lora-gateway/esxp1302/main/packet_forwarder/lora_pkt_fwd.c

/*
 / _____)             _              | |
( (____  _____ ____ _| |_ _____  ____| |__
 \____ \| ___ |    (_   _) ___ |/ ___)  _ \
 _____) ) ____| | | || |_| ____( (___| | | |
(______/|_____)_|_|_| \__)_____)\____)_| |_|
  (C)2019 Semtech

Description:
    Configure Lora concentrator and forward packets to a server
    Use GPS for packet timestamping.
    Send a becon at a regular interval without server intervention

License: Revised BSD License, see LICENSE.TXT file include in the project
*/


/* fix an issue between POSIX and C99 */
#if __STDC_VERSION__ >= 199901L
    #define _XOPEN_SOURCE 600
#else
    #define _XOPEN_SOURCE 500
#endif

#include <stdint.h>         /* C99 types */
#include <stdbool.h>        /* bool type */
#include <stdio.h>          /* printf, fprintf, snprintf, fopen, fputs */
#include <inttypes.h>       /* PRIx64, PRIu64... */

#include <string.h>         /* memset */
#include <signal.h>         /* sigaction */
#include <time.h>           /* time, clock_gettime, strftime, gmtime */
#include <sys/time.h>       /* timeval */
#include <unistd.h>         /* getopt, access */
#include <stdlib.h>         /* atoi, exit */
#include <errno.h>          /* error messages */
#include <math.h>           /* modf */

#include <sys/socket.h>     /* socket specific definitions */
#include <netinet/in.h>     /* INET constants and stuff */
#include <arpa/inet.h>      /* IP address conversion stuff */
#include <netdb.h>          /* gai_strerror */

#include <pthread.h>

#include "trace.h"
#include "jitqueue.h"
#include "parson.h"
#include "base64.h"
#include "loragw_hal.h"
#include "loragw_aux.h"
#include "loragw_reg.h"
#include "loragw_gps.h"
#include "loragw_gpio.h"

/// For ESP32
#include "freertos/FreeRTOS.h"
#include "freertos/task.h"
#include "freertos/semphr.h"
#include "freertos/event_groups.h"
#include "esp_system.h"
#include "esp_wifi.h"
#include "esp_event.h"
#include "esp_log.h"
#include "esp_err.h"
#include "nvs_flash.h"
#include "esp_console.h"
#include "argtable3/argtable3.h"
#include "esp_netif.h"
#include "esp_timer.h"
#include "esp_mac.h"
#include "esp_rom_gpio.h"
#include "mqtt_client.h"

#include "lwip/err.h"
#include "lwip/sys.h"
#include "lwip/sockets.h"
#include <lwip/netdb.h>
#include "esp_sntp.h"

#include "global_json.h"
#include "driver/gpio.h"

#include "http_server.h"
#include "led_indication.h"
#include "ioe.h"
#include "web_config.h"
#include "loragw_version.h"


#define ARRAY_SIZE(a)   (sizeof(a) / sizeof((a)[0]))
#define STRINGIFY(x)    #x
#define STR(x)          STRINGIFY(x)

#define RAND_RANGE(min, max) (rand() % (max + 1 - min) + min)

#ifndef VERSION_STRING
    #define VERSION_STRING "undefined"
#endif

#define JSON_CONF_DEFAULT   "global_conf.json"

#define DEFAULT_SERVER      127.0.0.1   /* hostname also supported */
#define DEFAULT_PORT_UP     1780
#define DEFAULT_PORT_DW     1782
#define DEFAULT_KEEPALIVE   5           /* default time interval for downstream keep-alive packet */
#define DEFAULT_STAT        30          /* default time interval for statistics */
#define PUSH_TIMEOUT_MS     100
#define PULL_TIMEOUT_MS     200
#define GPS_REF_MAX_AGE     30          /* maximum admitted delay in seconds of GPS loss before considering latest GPS sync unusable */
#define FETCH_SLEEP_MS      10          /* nb of ms waited when a fetch return no packets */
#define BEACON_POLL_MS      50          /* time in ms between polling of beacon TX status */

#define PROTOCOL_VERSION    2           /* v1.6 */
#define PROTOCOL_JSON_RXPK_FRAME_FORMAT 1

#define XERR_INIT_AVG       16          /* nb of measurements the XTAL correction is averaged on as initial value */
#define XERR_FILT_COEF      256         /* coefficient for low-pass XTAL error tracking */

#define PKT_PUSH_DATA   0
#define PKT_PUSH_ACK    1
#define PKT_PULL_DATA   2
#define PKT_PULL_RESP   3
#define PKT_PULL_ACK    4
#define PKT_TX_ACK      5

#define NB_PKT_MAX      24 /* max number of packets per fetch/send cycle */

#define MIN_LORA_PREAMB 6 /* minimum Lora preamble length for this application */
#define STD_LORA_PREAMB 8
#define MIN_FSK_PREAMB  3 /* minimum FSK preamble length for this application */
#define STD_FSK_PREAMB  5

#define STATUS_SIZE     200
#define TX_BUFF_SIZE    ((540 * NB_PKT_MAX) + 30 + STATUS_SIZE)
#define ACK_BUFF_SIZE   64

#define UNIX_GPS_EPOCH_OFFSET 315964800 /* Number of seconds ellapsed between 01.Jan.1970 00:00:00
                                                                          and 06.Jan.1980 00:00:00 */

#define DEFAULT_BEACON_FREQ_HZ      869525000
#define DEFAULT_BEACON_FREQ_NB      1
#define DEFAULT_BEACON_FREQ_STEP    0
#define DEFAULT_BEACON_DATARATE     9
#define DEFAULT_BEACON_BW_HZ        125000
#define DEFAULT_BEACON_POWER        14
#define DEFAULT_BEACON_INFODESC     0


/* for buttons on the bottom board */
#ifndef USER_BUTTON_1
#define USER_BUTTON_1    23
#endif

#ifndef USER_BUTTON_2
#define USER_BUTTON_2    25
#endif

#define BUTTON_PRESSED    0
#define BUTTON_RELEASED   1

/* for wifi configures */
#define ESP_WIFI_SSID      "esp32"
#define ESP_WIFI_PASS      "esp32wifi"
#define ESP_WIFI_CHANNEL   1
#define MAX_STA_CONN       4

#define WIFI_MAXIMUM_RETRY  5

/* The event group allows multiple bits for each event, but we only care about two events:
 * - we are connected to the AP with an IP
 * - we failed to connect after the maximum amount of retries */
#define WIFI_CONNECTED_BIT BIT0
#define WIFI_FAIL_BIT      BIT1

/* for display info on screen */
#ifndef BLINK_GPIO
#define BLINK_GPIO      2
#endif

#define TIME_REFRESH    5  // display the time on screen every 5s
#define N_CHAR_A_ROW    21  // max chars in a row is 21 in oled display mode=1

#define IP_LEN  32  // a right ip address should be no more than 16 bytes. some extra space for failed solving

#define MQTT_BROKER_URL "mqtt://192.168.1.202"
#define MQTT_TOPIC "/topic/esxp1302"


/* FreeRTOS event group to signal when we are connected*/
static EventGroupHandle_t s_wifi_event_group;

extern config_s config[CONFIG_NUM];
bool wifi_ready = false;
char wifi_ssid[32];
char wifi_pswd[64];
char udp_host[64];
char udp_port_str[16];
char self_ip[16] = "(unknown)";
char gw_id[32];
unsigned int udp_port;
unsigned int time_count = 0;  // used for display time on screen

// buffer for display output
char out_info[96];

static const char *BOOT_TAG = "gateway boot";
static const char *PKT_TAG = "packet-forward";
static const char *WIFI_TAG = "wifi station";
static const char *MQTT_TAG = "esxp1302_mqtt";

static esp_mqtt_client_handle_t mqtt_client;

/* spectral scan */
typedef struct spectral_scan_s {
    bool enable;            /* enable spectral scan thread */
    unsigned int freq_hz_start; /* first channel frequency, in Hz */
    uint8_t nb_chan;        /* number of channels to scan (200kHz between each channel) */
    uint16_t nb_scan;       /* number of scan points for each frequency scan */
    unsigned int pace_s;        /* number of seconds between 2 scans in the thread */
} spectral_scan_t;


/* signal handling variables */
volatile bool exit_sig = false; /* 1 -> application terminates cleanly (shut down hardware, close open files, etc) */
volatile bool quit_sig = false; /* 1 -> application terminates without shutting down the hardware */

/* packets filtering configuration variables */
static bool fwd_valid_pkt = true; /* packets with PAYLOAD CRC OK are forwarded */
static bool fwd_error_pkt = false; /* packets with PAYLOAD CRC ERROR are NOT forwarded */
static bool fwd_nocrc_pkt = false; /* packets with NO PAYLOAD CRC are NOT forwarded */

/* network configuration variables */
static uint64_t lgwm = 0; /* Lora gateway MAC address */
static char serv_addr[64] = STR(DEFAULT_SERVER); /* address of the server (host name or IPv4/IPv6) */
static char serv_port_up[8] = STR(DEFAULT_PORT_UP); /* server port for upstream traffic */
static char serv_port_down[8] = STR(DEFAULT_PORT_DW); /* server port for downstream traffic */
static int keepalive_time = DEFAULT_KEEPALIVE; /* send a PULL_DATA request every X seconds, negative = disabled */

/* statistics collection configuration variables */
static unsigned stat_interval = DEFAULT_STAT; /* time interval (in sec) at which statistics are collected and displayed */

/* gateway <-> MAC protocol variables */
static unsigned int net_mac_h; /* Most Significant Nibble, network order */
static unsigned int net_mac_l; /* Least Significant Nibble, network order */

/* network sockets */
static int sock_up; /* socket for upstream traffic */
static int sock_down; /* socket for downstream traffic */
struct sockaddr_in dest_addr;
struct sockaddr_in source_addr;

/* network protocol variables */
static struct timeval push_timeout_half = {0, (PUSH_TIMEOUT_MS * 500)}; /* cut in half, critical for throughput */
static struct timeval pull_timeout = {0, (PULL_TIMEOUT_MS * 1000)}; /* non critical for throughput */

/* hardware access control and correction */
SemaphoreHandle_t mx_concent; /* control access to the concentrator */
static SemaphoreHandle_t mx_xcorr; /* control access to the XTAL correction */
static bool xtal_correct_ok = false; /* set true when XTAL correction is stable enough */
static double xtal_correct = 1.0;

/* GPS configuration and synchronization */
static uart_port_t gps_uart_num = UART_NUM_1; /* uart port number for GPS */
static bool gps_enabled = false; /* is GPS enabled on that gateway ? */

/* GPS time reference */
static SemaphoreHandle_t mx_timeref; /* control access to GPS time reference */
static bool gps_ref_valid; /* is GPS reference acceptable (ie. not too old) */
static struct tref time_reference_gps; /* time reference used for GPS <-> timestamp conversion */

/* Reference coordinates, for broadcasting (beacon) */
static struct coord_s reference_coord;

/* Enable faking the GPS coordinates of the gateway */
static bool gps_fake_enable; /* enable the feature */

/* measurements to establish statistics */
static SemaphoreHandle_t mx_meas_up; /* control access to the upstream measurements */
static unsigned int meas_nb_rx_rcv = 0; /* count packets received */
static unsigned int meas_nb_rx_ok = 0; /* count packets received with PAYLOAD CRC OK */
static unsigned int meas_nb_rx_bad = 0; /* count packets received with PAYLOAD CRC ERROR */
static unsigned int meas_nb_rx_nocrc = 0; /* count packets received with NO PAYLOAD CRC */
static unsigned int meas_up_pkt_fwd = 0; /* number of radio packet forwarded to the server */
static unsigned int meas_up_network_byte = 0; /* sum of UDP bytes sent for upstream traffic */
static unsigned int meas_up_payload_byte = 0; /* sum of radio payload bytes sent for upstream traffic */
static unsigned int meas_up_dgram_sent = 0; /* number of datagrams sent for upstream traffic */
static unsigned int meas_up_ack_rcv = 0; /* number of datagrams acknowledged for upstream traffic */

static SemaphoreHandle_t mx_meas_dw; /* control access to the downstream measurements */
static unsigned int meas_dw_pull_sent = 0; /* number of PULL requests sent for downstream traffic */
static unsigned int meas_dw_ack_rcv = 0; /* number of PULL requests acknowledged for downstream traffic */
static unsigned int meas_dw_dgram_rcv = 0; /* count PULL response packets received for downstream traffic */
static unsigned int meas_dw_network_byte = 0; /* sum of UDP bytes sent for upstream traffic */
static unsigned int meas_dw_payload_byte = 0; /* sum of radio payload bytes sent for upstream traffic */
static unsigned int meas_nb_tx_ok = 0; /* count packets emitted successfully */
static unsigned int meas_nb_tx_fail = 0; /* count packets were TX failed for other reasons */
static unsigned int meas_nb_tx_requested = 0; /* count TX request from server (downlinks) */
static unsigned int meas_nb_tx_rejected_collision_packet = 0; /* count packets were TX request were rejected due to collision with another packet already programmed */
static unsigned int meas_nb_tx_rejected_collision_beacon = 0; /* count packets were TX request were rejected due to collision with a beacon already programmed */
static unsigned int meas_nb_tx_rejected_too_late = 0; /* count packets were TX request were rejected because it is too late to program it */
static unsigned int meas_nb_tx_rejected_too_early = 0; /* count packets were TX request were rejected because timestamp is too much in advance */
static unsigned int meas_nb_beacon_queued = 0; /* count beacon inserted in jit queue */
static unsigned int meas_nb_beacon_sent = 0; /* count beacon actually sent to concentrator */
static unsigned int meas_nb_beacon_rejected = 0; /* count beacon rejected for queuing */

static SemaphoreHandle_t mx_meas_gps; /* control access to the GPS statistics */
static bool gps_coord_valid; /* could we get valid GPS coordinates ? */
static struct coord_s meas_gps_coord; /* GPS position of the gateway */

static SemaphoreHandle_t mx_stat_rep; /* control access to the status report */
static bool report_ready = false; /* true when there is a new report to send to the server */
static char status_report[STATUS_SIZE]; /* status report as a JSON object */

/* beacon parameters */
static unsigned int beacon_period = 0; /* set beaconing period, must be a sub-multiple of 86400, the nb of sec in a day */
static unsigned int beacon_freq_hz = DEFAULT_BEACON_FREQ_HZ; /* set beacon TX frequency, in Hz */
static uint8_t beacon_freq_nb = DEFAULT_BEACON_FREQ_NB; /* set number of beaconing channels beacon */
static unsigned int beacon_freq_step = DEFAULT_BEACON_FREQ_STEP; /* set frequency step between beacon channels, in Hz */
static uint8_t beacon_datarate = DEFAULT_BEACON_DATARATE; /* set beacon datarate (SF) */
static unsigned int beacon_bw_hz = DEFAULT_BEACON_BW_HZ; /* set beacon bandwidth, in Hz */
static int8_t beacon_power = DEFAULT_BEACON_POWER; /* set beacon TX power, in dBm */
static uint8_t beacon_infodesc = DEFAULT_BEACON_INFODESC; /* set beacon information descriptor */

/* auto-quit function */
static unsigned int autoquit_threshold = 0; /* enable auto-quit after a number of non-acknowledged PULL_DATA (0 = disabled)*/

/* Just In Time TX scheduling */
static struct jit_queue_s jit_queue[LGW_RF_CHAIN_NB];

/* Gateway specificities */
static int8_t antenna_gain = 0;

/* TX capabilities */
static struct lgw_tx_gain_lut_s txlut[LGW_RF_CHAIN_NB]; /* TX gain table */
static unsigned int tx_freq_min[LGW_RF_CHAIN_NB]; /* lowest frequency supported by TX chain */
static unsigned int tx_freq_max[LGW_RF_CHAIN_NB]; /* highest frequency supported by TX chain */
static bool tx_enable[LGW_RF_CHAIN_NB] = {false}; /* Is TX enabled for a given RF chain ? */

static unsigned int nb_pkt_log[LGW_IF_CHAIN_NB][8]; /* [CH][SF] */
static unsigned int nb_pkt_received_lora = 0;
static unsigned int nb_pkt_received_fsk = 0;

static struct lgw_conf_debug_s debugconf;
static unsigned int nb_pkt_received_ref[16];

/* Interface type */
static lgw_com_type_t com_type = LGW_COM_SPI;

/* Spectral Scan */
static spectral_scan_t spectral_scan_params = {
    .enable = false,
    .freq_hz_start = 0,
    .nb_chan = 0,
    .nb_scan = 0,
    .pace_s = 10
};

TaskHandle_t pJit;
TaskHandle_t pThreadUp;
TaskHandle_t pLed;
TaskHandle_t pkt_fwd_handle;
TaskHandle_t mqtt_handle;
TaskHandle_t gps_handle;
TaskHandle_t valid_handle;


//static void sig_handler(int sigio);

static int parse_SX130x_configuration(const char * conf_array);

static int parse_gateway_configuration(const char * conf_array);

static int parse_debug_configuration(const char * conf_array);

static uint16_t crc16(const uint8_t * data, unsigned size);

static double difftimespec(struct timespec end, struct timespec beginning);

static void gps_process_sync(void);

static void gps_process_coords(void);

static int get_tx_gain_lut_index(uint8_t rf_chain, int8_t rf_power, uint8_t * lut_index);

/* threads */
void thread_up(void);
void thread_down(void);
void thread_jit(void);
void thread_gps(void);
void thread_valid(void);
void thread_spectral_scan(void);


/*
static void sig_handler(int sigio) {
    if (sigio == SIGQUIT) {
        quit_sig = true;
    } else if ((sigio == SIGINT) || (sigio == SIGTERM)) {
        exit_sig = true;
    }
    return;
}
*/

void Init_Led( void )
{
    esp_rom_gpio_pad_select_gpio( LED_BLUE_GPIO );
    esp_rom_gpio_pad_select_gpio( LED_GREEN_GPIO );
    esp_rom_gpio_pad_select_gpio( LED_RED_GPIO );
    gpio_set_direction( LED_BLUE_GPIO, GPIO_MODE_OUTPUT );
    gpio_set_direction( LED_GREEN_GPIO, GPIO_MODE_OUTPUT );
    gpio_set_direction( LED_RED_GPIO, GPIO_MODE_OUTPUT );
    gpio_set_level( LED_BLUE_GPIO, 1 );   // Default state
    gpio_set_level( LED_GREEN_GPIO, 1 );   // Default state
    gpio_set_level( LED_RED_GPIO, 1 );   // Default state
}

static void oled_show_one_line(uint8_t x, uint8_t y, char *str, uint8_t text_size)
{
    char *p = str;
    int len = strlen(str);
    char buf[N_CHAR_A_ROW + 1] = "                     ";  // 21 ' 's

    if(len < N_CHAR_A_ROW){
        strncpy(buf, str, len);
        p = buf;
    }
    oled_show_str(x, y, p, text_size);
}


static int parse_SX130x_configuration(const char * conf_array) {
    int i, j, number;
    char param_name[40]; /* used to generate variable parameter names */
    const char *str; /* used to store string value from JSON object */
    const char conf_obj_name[] = "SX130x_conf";
    JSON_Value *root_val = NULL;
    JSON_Value *val = NULL;
    JSON_Object *conf_obj = NULL;
    JSON_Object *conf_txgain_obj;
    JSON_Object *conf_ts_obj;
    JSON_Object *conf_sx1261_obj = NULL;
    JSON_Object *conf_scan_obj = NULL;
    JSON_Object *conf_lbt_obj = NULL;
    JSON_Object *conf_lbtchan_obj = NULL;
    JSON_Array *conf_txlut_array = NULL;
    JSON_Array *conf_lbtchan_array = NULL;
    JSON_Array *conf_demod_array = NULL;

    struct lgw_conf_board_s boardconf;
    struct lgw_conf_rxrf_s rfconf;
    struct lgw_conf_rxif_s ifconf;
    struct lgw_conf_demod_s demodconf;
    struct lgw_conf_ftime_s tsconf;
    struct lgw_conf_sx1261_s sx1261conf;
    unsigned int sf, bw, fdev;
    bool sx1250_tx_lut;
    size_t size;

    /* try to parse JSON */
    root_val = json_parse_array_with_comments(conf_array);
    if (root_val == NULL) {
        MSG("ERROR: conf array is not a valid JSON string\n");
        exit(EXIT_FAILURE);
    }

    /* point to the gateway configuration object */
    conf_obj = json_object_get_object(json_value_get_object(root_val), conf_obj_name);
    if (conf_obj == NULL) {
        MSG("INFO: conf array does not contain a JSON object named %s\n", conf_obj_name);
        return -1;
    } else {
        MSG("INFO: conf array does contain a JSON object named %s, parsing SX1302 parameters\n", conf_obj_name);
    }

    /* set board configuration */
    memset(&boardconf, 0, sizeof boardconf); /* initialize configuration structure */
    str = json_object_get_string(conf_obj, "com_type");
    if (str == NULL) {
        MSG("ERROR: com_type must be configured in conf array\n");
        return -1;
    } else if (!strncmp(str, "SPI", 3) || !strncmp(str, "spi", 3)) {
        boardconf.com_type = LGW_COM_SPI;
    } else if (!strncmp(str, "USB", 3) || !strncmp(str, "usb", 3)) {
        boardconf.com_type = LGW_COM_USB;
    } else {
        MSG("ERROR: invalid com type: %s (should be SPI or USB)\n", str);
        return -1;
    }
    com_type = boardconf.com_type;
    str = json_object_get_string(conf_obj, "com_path");
    if (str != NULL) {
        strncpy(boardconf.com_path, str, sizeof boardconf.com_path);
        boardconf.com_path[sizeof boardconf.com_path - 1] = '\0'; /* ensure string termination */
    } else {
        MSG("ERROR: com_path must be configured in conf array\n");
        return -1;
    }
    val = json_object_get_value(conf_obj, "lorawan_public"); /* fetch value (if possible) */
    if (json_value_get_type(val) == JSONBoolean) {
        boardconf.lorawan_public = (bool)json_value_get_boolean(val);
    } else {
        MSG("WARNING: Data type for lorawan_public seems wrong, please check\n");
        boardconf.lorawan_public = false;
    }
    val = json_object_get_value(conf_obj, "clksrc"); /* fetch value (if possible) */
    if (json_value_get_type(val) == JSONNumber) {
        boardconf.clksrc = (uint8_t)json_value_get_number(val);
    } else {
        MSG("WARNING: Data type for clksrc seems wrong, please check\n");
        boardconf.clksrc = 0;
    }
    val = json_object_get_value(conf_obj, "full_duplex"); /* fetch value (if possible) */
    if (json_value_get_type(val) == JSONBoolean) {
        boardconf.full_duplex = (bool)json_value_get_boolean(val);
    } else {
        MSG("WARNING: Data type for full_duplex seems wrong, please check\n");
        boardconf.full_duplex = false;
    }
    MSG("INFO: com_type %s, com_path %s, lorawan_public %d, clksrc %d, full_duplex %d\n",
            (boardconf.com_type == LGW_COM_SPI) ? "SPI" : "USB",
            boardconf.com_path, boardconf.lorawan_public, boardconf.clksrc,
            boardconf.full_duplex);
    /* all parameters parsed, submitting configuration to the HAL */
    if (lgw_board_setconf(&boardconf) != LGW_HAL_SUCCESS) {
        MSG("ERROR: Failed to configure board\n");
        return -1;
    }

    /* set antenna gain configuration */
    val = json_object_get_value(conf_obj, "antenna_gain"); /* fetch value (if possible) */
    if (val != NULL) {
        if (json_value_get_type(val) == JSONNumber) {
            antenna_gain = (int8_t)json_value_get_number(val);
        } else {
            MSG("WARNING: Data type for antenna_gain seems wrong, please check\n");
            antenna_gain = 0;
        }
    }
    MSG("INFO: antenna_gain %d dBi\n", antenna_gain);

    /* set timestamp configuration */
    conf_ts_obj = json_object_get_object(conf_obj, "fine_timestamp");
    if (conf_ts_obj == NULL) {
        MSG("INFO: conf array does not contain a JSON object for fine timestamp\n");
    } else {
        val = json_object_get_value(conf_ts_obj, "enable"); /* fetch value (if possible) */
        if (json_value_get_type(val) == JSONBoolean) {
            tsconf.enable = (bool)json_value_get_boolean(val);
        } else {
            MSG("WARNING: Data type for fine_timestamp.enable seems wrong, please check\n");
            tsconf.enable = false;
        }
        if (tsconf.enable == true) {
            str = json_object_get_string(conf_ts_obj, "mode");
            if (str == NULL) {
                MSG("ERROR: fine_timestamp.mode must be configured in conf array\n");
                return -1;
            } else if (!strncmp(str, "high_capacity", 13) || !strncmp(str, "HIGH_CAPACITY", 13)) {
                tsconf.mode = LGW_FTIME_MODE_HIGH_CAPACITY;
            } else if (!strncmp(str, "all_sf", 6) || !strncmp(str, "ALL_SF", 6)) {
                tsconf.mode = LGW_FTIME_MODE_ALL_SF;
            } else {
                MSG("ERROR: invalid fine timestamp mode: %s (should be high_capacity or all_sf)\n", str);
                return -1;
            }
            MSG("INFO: Configuring fine timestamp with %s mode\n", str);

            /* all parameters parsed, submitting configuration to the HAL */
            if (lgw_ftime_setconf(&tsconf) != LGW_HAL_SUCCESS) {
                MSG("ERROR: Failed to configure fine timestamp\n");
                return -1;
            }
        } else {
            MSG("INFO: Configuring legacy timestamp\n");
        }
    }

    /* set SX1261 configuration */
    memset(&sx1261conf, 0, sizeof sx1261conf); /* initialize configuration structure */
    conf_sx1261_obj = json_object_get_object(conf_obj, "sx1261_conf"); /* fetch value (if possible) */
    if (conf_sx1261_obj == NULL) {
        MSG("INFO: no configuration for SX1261\n");
    } else {
        /* Global SX1261 configuration */
        str = json_object_get_string(conf_sx1261_obj, "spi_path");
        if (str != NULL) {
            strncpy(sx1261conf.spi_path, str, sizeof sx1261conf.spi_path);
            sx1261conf.spi_path[sizeof sx1261conf.spi_path - 1] = '\0'; /* ensure string termination */
        } else {
            MSG("INFO: SX1261 spi_path is not configured in conf array\n");
        }
        val = json_object_get_value(conf_sx1261_obj, "rssi_offset"); /* fetch value (if possible) */
        if (json_value_get_type(val) == JSONNumber) {
            sx1261conf.rssi_offset = (int8_t)json_value_get_number(val);
        } else {
            MSG("WARNING: Data type for sx1261_conf.rssi_offset seems wrong, please check\n");
            sx1261conf.rssi_offset = 0;
        }

        /* Spectral Scan configuration */
        conf_scan_obj = json_object_get_object(conf_sx1261_obj, "spectral_scan"); /* fetch value (if possible) */
        if (conf_scan_obj == NULL) {
            MSG("INFO: no configuration for Spectral Scan\n");
        } else {
            val = json_object_get_value(conf_scan_obj, "enable"); /* fetch value (if possible) */
            if (json_value_get_type(val) == JSONBoolean) {
                /* Enable background spectral scan thread in packet forwarder */
                spectral_scan_params.enable = (bool)json_value_get_boolean(val);
            } else {
                MSG("WARNING: Data type for spectral_scan.enable seems wrong, please check\n");
            }
            if (spectral_scan_params.enable == true) {
                /* Enable the sx1261 radio hardware configuration to allow spectral scan */
                sx1261conf.enable = true;
                MSG("INFO: Spectral Scan with SX1261 is enabled\n");

                /* Get Spectral Scan Parameters */
                val = json_object_get_value(conf_scan_obj, "freq_start"); /* fetch value (if possible) */
                if (json_value_get_type(val) == JSONNumber) {
                    spectral_scan_params.freq_hz_start = (unsigned int)json_value_get_number(val);
                } else {
                    MSG("WARNING: Data type for spectral_scan.freq_start seems wrong, please check\n");
                }
                val = json_object_get_value(conf_scan_obj, "nb_chan"); /* fetch value (if possible) */
                if (json_value_get_type(val) == JSONNumber) {
                    spectral_scan_params.nb_chan = (uint8_t)json_value_get_number(val);
                } else {
                    MSG("WARNING: Data type for spectral_scan.nb_chan seems wrong, please check\n");
                }
                val = json_object_get_value(conf_scan_obj, "nb_scan"); /* fetch value (if possible) */
                if (json_value_get_type(val) == JSONNumber) {
                    spectral_scan_params.nb_scan = (uint16_t)json_value_get_number(val);
                } else {
                    MSG("WARNING: Data type for spectral_scan.nb_scan seems wrong, please check\n");
                }
                val = json_object_get_value(conf_scan_obj, "pace_s"); /* fetch value (if possible) */
                if (json_value_get_type(val) == JSONNumber) {
                    spectral_scan_params.pace_s = (unsigned int)json_value_get_number(val);
                } else {
                    MSG("WARNING: Data type for spectral_scan.pace_s seems wrong, please check\n");
                }
            }
        }

        /* LBT configuration */
        conf_lbt_obj = json_object_get_object(conf_sx1261_obj, "lbt"); /* fetch value (if possible) */
        if (conf_lbt_obj == NULL) {
            MSG("INFO: no configuration for LBT\n");
        } else {
            val = json_object_get_value(conf_lbt_obj, "enable"); /* fetch value (if possible) */
            if (json_value_get_type(val) == JSONBoolean) {
                sx1261conf.lbt_conf.enable = (bool)json_value_get_boolean(val);
            } else {
                MSG("WARNING: Data type for lbt.enable seems wrong, please check\n");
            }
            if (sx1261conf.lbt_conf.enable == true) {
                /* Enable the sx1261 radio hardware configuration to allow spectral scan */
                sx1261conf.enable = true;
                MSG("INFO: Listen-Before-Talk with SX1261 is enabled\n");

                val = json_object_get_value(conf_lbt_obj, "rssi_target"); /* fetch value (if possible) */
                if (json_value_get_type(val) == JSONNumber) {
                    sx1261conf.lbt_conf.rssi_target = (int8_t)json_value_get_number(val);
                } else {
                    MSG("WARNING: Data type for lbt.rssi_target seems wrong, please check\n");
                    sx1261conf.lbt_conf.rssi_target = 0;
                }
                /* set LBT channels configuration */
                conf_lbtchan_array = json_object_get_array(conf_lbt_obj, "channels");
                if (conf_lbtchan_array != NULL) {
                    sx1261conf.lbt_conf.nb_channel = json_array_get_count(conf_lbtchan_array);
                    MSG("INFO: %u LBT channels configured\n", sx1261conf.lbt_conf.nb_channel);
                }
                for (i = 0; i < (int)sx1261conf.lbt_conf.nb_channel; i++) {
                    /* Sanity check */
                    if (i >= LGW_LBT_CHANNEL_NB_MAX) {
                        MSG("ERROR: LBT channel %d not supported, skip it\n", i);
                        break;
                    }
                    /* Get LBT channel configuration object from array */
                    conf_lbtchan_obj = json_array_get_object(conf_lbtchan_array, i);

                    /* Channel frequency */
                    val = json_object_dotget_value(conf_lbtchan_obj, "freq_hz"); /* fetch value (if possible) */
                    if (val != NULL) {
                        if (json_value_get_type(val) == JSONNumber) {
                            sx1261conf.lbt_conf.channels[i].freq_hz = (unsigned int)json_value_get_number(val);
                        } else {
                            MSG("WARNING: Data type for lbt.channels[%d].freq_hz seems wrong, please check\n", i);
                            sx1261conf.lbt_conf.channels[i].freq_hz = 0;
                        }
                    } else {
                        MSG("ERROR: no frequency defined for LBT channel %d\n", i);
                        return -1;
                    }

                    /* Channel bandiwdth */
                    val = json_object_dotget_value(conf_lbtchan_obj, "bandwidth"); /* fetch value (if possible) */
                    if (val != NULL) {
                        if (json_value_get_type(val) == JSONNumber) {
                            bw = (unsigned int)json_value_get_number(val);
                            switch(bw) {
                                case 500000: sx1261conf.lbt_conf.channels[i].bandwidth = BW_500KHZ; break;
                                case 250000: sx1261conf.lbt_conf.channels[i].bandwidth = BW_250KHZ; break;
                                case 125000: sx1261conf.lbt_conf.channels[i].bandwidth = BW_125KHZ; break;
                                default: sx1261conf.lbt_conf.channels[i].bandwidth = BW_UNDEFINED;
                            }
                        } else {
                            MSG("WARNING: Data type for lbt.channels[%d].freq_hz seems wrong, please check\n", i);
                            sx1261conf.lbt_conf.channels[i].bandwidth = BW_UNDEFINED;
                        }
                    } else {
                        MSG("ERROR: no bandiwdth defined for LBT channel %d\n", i);
                        return -1;
                    }

                    /* Channel scan time */
                    val = json_object_dotget_value(conf_lbtchan_obj, "scan_time_us"); /* fetch value (if possible) */
                    if (val != NULL) {
                        if (json_value_get_type(val) == JSONNumber) {
                            if ((uint16_t)json_value_get_number(val) == 128) {
                                sx1261conf.lbt_conf.channels[i].scan_time_us = LGW_LBT_SCAN_TIME_128_US;
                            } else if ((uint16_t)json_value_get_number(val) == 5000) {
                                sx1261conf.lbt_conf.channels[i].scan_time_us = LGW_LBT_SCAN_TIME_5000_US;
                            } else {
                                MSG("ERROR: scan time not supported for LBT channel %d, must be 128 or 5000\n", i);
                                return -1;
                            }
                        } else {
                            MSG("WARNING: Data type for lbt.channels[%d].scan_time_us seems wrong, please check\n", i);
                            sx1261conf.lbt_conf.channels[i].scan_time_us = 0;
                        }
                    } else {
                        MSG("ERROR: no scan_time_us defined for LBT channel %d\n", i);
                        return -1;
                    }

                    /* Channel transmit time */
                    val = json_object_dotget_value(conf_lbtchan_obj, "transmit_time_ms"); /* fetch value (if possible) */
                    if (val != NULL) {
                        if (json_value_get_type(val) == JSONNumber) {
                            sx1261conf.lbt_conf.channels[i].transmit_time_ms = (uint16_t)json_value_get_number(val);
                        } else {
                            MSG("WARNING: Data type for lbt.channels[%d].transmit_time_ms seems wrong, please check\n", i);
                            sx1261conf.lbt_conf.channels[i].transmit_time_ms = 0;
                        }
                    } else {
                        MSG("ERROR: no transmit_time_ms defined for LBT channel %d\n", i);
                        return -1;
                    }
                }
            }
        }

        /* all parameters parsed, submitting configuration to the HAL */
        if (lgw_sx1261_setconf(&sx1261conf) != LGW_HAL_SUCCESS) {
            MSG("ERROR: Failed to configure the SX1261 radio\n");
            return -1;
        }
    }

    /* set configuration for RF chains */
    for (i = 0; i < LGW_RF_CHAIN_NB; ++i) {
        memset(&rfconf, 0, sizeof rfconf); /* initialize configuration structure */
        snprintf(param_name, sizeof param_name, "radio_%i", i); /* compose parameter path inside JSON structure */
        val = json_object_get_value(conf_obj, param_name); /* fetch value (if possible) */
        if (json_value_get_type(val) != JSONObject) {
            MSG("INFO: no configuration for radio %i\n", i);
            continue;
        }
        /* there is an object to configure that radio, let's parse it */
        snprintf(param_name, sizeof param_name, "radio_%i.enable", i);
        val = json_object_dotget_value(conf_obj, param_name);
        if (json_value_get_type(val) == JSONBoolean) {
            rfconf.enable = (bool)json_value_get_boolean(val);
        } else {
            rfconf.enable = false;
        }
        if (rfconf.enable == false) { /* radio disabled, nothing else to parse */
            MSG("INFO: radio %i disabled\n", i);
        } else  { /* radio enabled, will parse the other parameters */
            snprintf(param_name, sizeof param_name, "radio_%i.freq", i);
            rfconf.freq_hz = (unsigned int)json_object_dotget_number(conf_obj, param_name);
            snprintf(param_name, sizeof param_name, "radio_%i.rssi_offset", i);
            rfconf.rssi_offset = (float)json_object_dotget_number(conf_obj, param_name);
            snprintf(param_name, sizeof param_name, "radio_%i.rssi_tcomp.coeff_a", i);
            rfconf.rssi_tcomp.coeff_a = (float)json_object_dotget_number(conf_obj, param_name);
            snprintf(param_name, sizeof param_name, "radio_%i.rssi_tcomp.coeff_b", i);
            rfconf.rssi_tcomp.coeff_b = (float)json_object_dotget_number(conf_obj, param_name);
            snprintf(param_name, sizeof param_name, "radio_%i.rssi_tcomp.coeff_c", i);
            rfconf.rssi_tcomp.coeff_c = (float)json_object_dotget_number(conf_obj, param_name);
            snprintf(param_name, sizeof param_name, "radio_%i.rssi_tcomp.coeff_d", i);
            rfconf.rssi_tcomp.coeff_d = (float)json_object_dotget_number(conf_obj, param_name);
            snprintf(param_name, sizeof param_name, "radio_%i.rssi_tcomp.coeff_e", i);
            rfconf.rssi_tcomp.coeff_e = (float)json_object_dotget_number(conf_obj, param_name);
            snprintf(param_name, sizeof param_name, "radio_%i.type", i);
            str = json_object_dotget_string(conf_obj, param_name);
            if (!strncmp(str, "SX1255", 6)) {
                rfconf.type = LGW_RADIO_TYPE_SX1255;
            } else if (!strncmp(str, "SX1257", 6)) {
                rfconf.type = LGW_RADIO_TYPE_SX1257;
            } else if (!strncmp(str, "SX1250", 6)) {
                rfconf.type = LGW_RADIO_TYPE_SX1250;
            } else {
                MSG("WARNING: invalid radio type: %s (should be SX1255 or SX1257 or SX1250)\n", str);
            }
            snprintf(param_name, sizeof param_name, "radio_%i.single_input_mode", i);
            val = json_object_dotget_value(conf_obj, param_name);
            if (json_value_get_type(val) == JSONBoolean) {
                rfconf.single_input_mode = (bool)json_value_get_boolean(val);
            } else {
                rfconf.single_input_mode = false;
            }

            snprintf(param_name, sizeof param_name, "radio_%i.tx_enable", i);
            val = json_object_dotget_value(conf_obj, param_name);
            if (json_value_get_type(val) == JSONBoolean) {
                rfconf.tx_enable = (bool)json_value_get_boolean(val);
                tx_enable[i] = rfconf.tx_enable; /* update global context for later check */
                if (rfconf.tx_enable == true) {
                    /* tx is enabled on this rf chain, we need its frequency range */
                    snprintf(param_name, sizeof param_name, "radio_%i.tx_freq_min", i);
                    tx_freq_min[i] = (unsigned int)json_object_dotget_number(conf_obj, param_name);
                    snprintf(param_name, sizeof param_name, "radio_%i.tx_freq_max", i);
                    tx_freq_max[i] = (unsigned int)json_object_dotget_number(conf_obj, param_name);
                    if ((tx_freq_min[i] == 0) || (tx_freq_max[i] == 0)) {
                        MSG("WARNING: no frequency range specified for TX rf chain %d\n", i);
                    }

                    /* set configuration for tx gains */
                    memset(&txlut[i], 0, sizeof txlut[i]); /* initialize configuration structure */
                    snprintf(param_name, sizeof param_name, "radio_%i.tx_gain_lut", i);
                    conf_txlut_array = json_object_dotget_array(conf_obj, param_name);
                    if (conf_txlut_array != NULL) {
                        txlut[i].size = json_array_get_count(conf_txlut_array);
                        /* Detect if we have a sx125x or sx1250 configuration */
                        conf_txgain_obj = json_array_get_object(conf_txlut_array, 0);
                        val = json_object_dotget_value(conf_txgain_obj, "pwr_idx");
                        if (val != NULL) {
                            printf("INFO: Configuring Tx Gain LUT for rf_chain %u with %u indexes for sx1250\n", i, txlut[i].size);
                            sx1250_tx_lut = true;
                        } else {
                            printf("INFO: Configuring Tx Gain LUT for rf_chain %u with %u indexes for sx125x\n", i, txlut[i].size);
                            sx1250_tx_lut = false;
                        }
                        /* Parse the table */
                        for (j = 0; j < (int)txlut[i].size; j++) {
                             /* Sanity check */
                            if (j >= TX_GAIN_LUT_SIZE_MAX) {
                                printf("ERROR: TX Gain LUT [%u] index %d not supported, skip it\n", i, j);
                                break;
                            }
                            /* Get TX gain object from LUT */
                            conf_txgain_obj = json_array_get_object(conf_txlut_array, j);
                            /* rf power */
                            val = json_object_dotget_value(conf_txgain_obj, "rf_power");
                            if (json_value_get_type(val) == JSONNumber) {
                                txlut[i].lut[j].rf_power = (int8_t)json_value_get_number(val);
                            } else {
                                printf("WARNING: Data type for %s[%d] seems wrong, please check\n", "rf_power", j);
                                txlut[i].lut[j].rf_power = 0;
                            }
                            /* PA gain */
                            val = json_object_dotget_value(conf_txgain_obj, "pa_gain");
                            if (json_value_get_type(val) == JSONNumber) {
                                txlut[i].lut[j].pa_gain = (uint8_t)json_value_get_number(val);
                            } else {
                                printf("WARNING: Data type for %s[%d] seems wrong, please check\n", "pa_gain", j);
                                txlut[i].lut[j].pa_gain = 0;
                            }
                            if (sx1250_tx_lut == false) {
                                /* DIG gain */
                                val = json_object_dotget_value(conf_txgain_obj, "dig_gain");
                                if (json_value_get_type(val) == JSONNumber) {
                                    txlut[i].lut[j].dig_gain = (uint8_t)json_value_get_number(val);
                                } else {
                                    printf("WARNING: Data type for %s[%d] seems wrong, please check\n", "dig_gain", j);
                                    txlut[i].lut[j].dig_gain = 0;
                                }
                                /* DAC gain */
                                val = json_object_dotget_value(conf_txgain_obj, "dac_gain");
                                if (json_value_get_type(val) == JSONNumber) {
                                    txlut[i].lut[j].dac_gain = (uint8_t)json_value_get_number(val);
                                } else {
                                    printf("WARNING: Data type for %s[%d] seems wrong, please check\n", "dac_gain", j);
                                    txlut[i].lut[j].dac_gain = 3; /* This is the only dac_gain supported for now */
                                }
                                /* MIX gain */
                                val = json_object_dotget_value(conf_txgain_obj, "mix_gain");
                                if (json_value_get_type(val) == JSONNumber) {
                                    txlut[i].lut[j].mix_gain = (uint8_t)json_value_get_number(val);
                                } else {
                                    printf("WARNING: Data type for %s[%d] seems wrong, please check\n", "mix_gain", j);
                                    txlut[i].lut[j].mix_gain = 0;
                                }
                            } else {
                                /* TODO: rework this, should not be needed for sx1250 */
                                txlut[i].lut[j].mix_gain = 5;

                                /* power index */
                                val = json_object_dotget_value(conf_txgain_obj, "pwr_idx");
                                if (json_value_get_type(val) == JSONNumber) {
                                    txlut[i].lut[j].pwr_idx = (uint8_t)json_value_get_number(val);
                                } else {
                                    printf("WARNING: Data type for %s[%d] seems wrong, please check\n", "pwr_idx", j);
                                    txlut[i].lut[j].pwr_idx = 0;
                                }
                            }
                        }
                        /* all parameters parsed, submitting configuration to the HAL */
                        if (txlut[i].size > 0) {
                            if (lgw_txgain_setconf(i, &txlut[i]) != LGW_HAL_SUCCESS) {
                                MSG("ERROR: Failed to configure concentrator TX Gain LUT for rf_chain %u\n", i);
                                return -1;
                            }
                        } else {
                            MSG("WARNING: No TX gain LUT defined for rf_chain %u\n", i);
                        }
                    } else {
                        MSG("WARNING: No TX gain LUT defined for rf_chain %u\n", i);
                    }
                }
            } else {
                rfconf.tx_enable = false;
            }
            MSG("INFO: radio %i enabled (type %s), center frequency %u, RSSI offset %f, tx enabled %d, single input mode %d\n",
                    i, str, rfconf.freq_hz, rfconf.rssi_offset, rfconf.tx_enable, rfconf.single_input_mode);
        }
        /* all parameters parsed, submitting configuration to the HAL */
        if (lgw_rxrf_setconf(i, &rfconf) != LGW_HAL_SUCCESS) {
            MSG("ERROR: invalid configuration for radio %i\n", i);
            return -1;
        }
    }

    /* set configuration for demodulators */
    memset(&demodconf, 0, sizeof demodconf); /* initialize configuration structure */
    val = json_object_get_value(conf_obj, "chan_multiSF_All"); /* fetch value (if possible) */
    if (json_value_get_type(val) != JSONObject) {
        MSG("INFO: no configuration for LoRa multi-SF spreading factors enabling\n");
    } else {
        conf_demod_array = json_object_dotget_array(conf_obj, "chan_multiSF_All.spreading_factor_enable");
        if ((conf_demod_array != NULL) && ((size = json_array_get_count(conf_demod_array)) <= LGW_MULTI_NB)) {
            for (i = 0; i < (int)size; i++) {
                number = json_array_get_number(conf_demod_array, i);
                if (number < 5 || number > 12) {
                    MSG("WARNING: failed to parse chan_multiSF_All.spreading_factor_enable (wrong value at idx %d)\n", i);
                    demodconf.multisf_datarate = 0xFF; /* enable all SFs */
                    break;
                } else {
                    /* set corresponding bit in the bitmask SF5 is LSB -> SF12 is MSB */
                    demodconf.multisf_datarate |= (1 << (number - 5));
                }
            }
        } else {
            MSG("WARNING: failed to parse chan_multiSF_All.spreading_factor_enable\n");
            demodconf.multisf_datarate = 0xFF; /* enable all SFs */
        }
        /* all parameters parsed, submitting configuration to the HAL */
        if (lgw_demod_setconf(&demodconf) != LGW_HAL_SUCCESS) {
            MSG("ERROR: invalid configuration for demodulation parameters\n");
            return -1;
        }
    }

    /* set configuration for Lora multi-SF channels (bandwidth cannot be set) */
    for (i = 0; i < LGW_MULTI_NB; ++i) {
        memset(&ifconf, 0, sizeof ifconf); /* initialize configuration structure */
        snprintf(param_name, sizeof param_name, "chan_multiSF_%i", i); /* compose parameter path inside JSON structure */
        val = json_object_get_value(conf_obj, param_name); /* fetch value (if possible) */
        if (json_value_get_type(val) != JSONObject) {
            MSG("INFO: no configuration for Lora multi-SF channel %i\n", i);
            continue;
        }
        /* there is an object to configure that Lora multi-SF channel, let's parse it */
        snprintf(param_name, sizeof param_name, "chan_multiSF_%i.enable", i);
        val = json_object_dotget_value(conf_obj, param_name);
        if (json_value_get_type(val) == JSONBoolean) {
            ifconf.enable = (bool)json_value_get_boolean(val);
        } else {
            ifconf.enable = false;
        }
        if (ifconf.enable == false) { /* Lora multi-SF channel disabled, nothing else to parse */
            MSG("INFO: Lora multi-SF channel %i disabled\n", i);
        } else  { /* Lora multi-SF channel enabled, will parse the other parameters */
            snprintf(param_name, sizeof param_name, "chan_multiSF_%i.radio", i);
            ifconf.rf_chain = (unsigned int)json_object_dotget_number(conf_obj, param_name);
            snprintf(param_name, sizeof param_name, "chan_multiSF_%i.if", i);
            ifconf.freq_hz = (int32_t)json_object_dotget_number(conf_obj, param_name);
            // TODO: handle individual SF enabling and disabling (spread_factor)
            MSG("INFO: Lora multi-SF channel %i>  radio %i, IF %i Hz, 125 kHz bw, SF 5 to 12\n", i, ifconf.rf_chain, ifconf.freq_hz);
        }
        /* all parameters parsed, submitting configuration to the HAL */
        if (lgw_rxif_setconf(i, &ifconf) != LGW_HAL_SUCCESS) {
            MSG("ERROR: invalid configuration for Lora multi-SF channel %i\n", i);
            return -1;
        }
    }

    /* set configuration for Lora standard channel */
    memset(&ifconf, 0, sizeof ifconf); /* initialize configuration structure */
    val = json_object_get_value(conf_obj, "chan_Lora_std"); /* fetch value (if possible) */
    if (json_value_get_type(val) != JSONObject) {
        MSG("INFO: no configuration for Lora standard channel\n");
    } else {
        val = json_object_dotget_value(conf_obj, "chan_Lora_std.enable");
        if (json_value_get_type(val) == JSONBoolean) {
            ifconf.enable = (bool)json_value_get_boolean(val);
        } else {
            ifconf.enable = false;
        }
        if (ifconf.enable == false) {
            MSG("INFO: Lora standard channel %i disabled\n", i);
        } else  {
            ifconf.rf_chain = (unsigned int)json_object_dotget_number(conf_obj, "chan_Lora_std.radio");
            ifconf.freq_hz = (int32_t)json_object_dotget_number(conf_obj, "chan_Lora_std.if");
            bw = (unsigned int)json_object_dotget_number(conf_obj, "chan_Lora_std.bandwidth");
            switch(bw) {
                case 500000: ifconf.bandwidth = BW_500KHZ; break;
                case 250000: ifconf.bandwidth = BW_250KHZ; break;
                case 125000: ifconf.bandwidth = BW_125KHZ; break;
                default: ifconf.bandwidth = BW_UNDEFINED;
            }
            sf = (unsigned int)json_object_dotget_number(conf_obj, "chan_Lora_std.spread_factor");
            switch(sf) {
                case  5: ifconf.datarate = DR_LORA_SF5;  break;
                case  6: ifconf.datarate = DR_LORA_SF6;  break;
                case  7: ifconf.datarate = DR_LORA_SF7;  break;
                case  8: ifconf.datarate = DR_LORA_SF8;  break;
                case  9: ifconf.datarate = DR_LORA_SF9;  break;
                case 10: ifconf.datarate = DR_LORA_SF10; break;
                case 11: ifconf.datarate = DR_LORA_SF11; break;
                case 12: ifconf.datarate = DR_LORA_SF12; break;
                default: ifconf.datarate = DR_UNDEFINED;
            }
            val = json_object_dotget_value(conf_obj, "chan_Lora_std.implicit_hdr");
            if (json_value_get_type(val) == JSONBoolean) {
                ifconf.implicit_hdr = (bool)json_value_get_boolean(val);
            } else {
                ifconf.implicit_hdr = false;
            }
            if (ifconf.implicit_hdr == true) {
                val = json_object_dotget_value(conf_obj, "chan_Lora_std.implicit_payload_length");
                if (json_value_get_type(val) == JSONNumber) {
                    ifconf.implicit_payload_length = (uint8_t)json_value_get_number(val);
                } else {
                    MSG("ERROR: payload length setting is mandatory for implicit header mode\n");
                    return -1;
                }
                val = json_object_dotget_value(conf_obj, "chan_Lora_std.implicit_crc_en");
                if (json_value_get_type(val) == JSONBoolean) {
                    ifconf.implicit_crc_en = (bool)json_value_get_boolean(val);
                } else {
                    MSG("ERROR: CRC enable setting is mandatory for implicit header mode\n");
                    return -1;
                }
                val = json_object_dotget_value(conf_obj, "chan_Lora_std.implicit_coderate");
                if (json_value_get_type(val) == JSONNumber) {
                    ifconf.implicit_coderate = (uint8_t)json_value_get_number(val);
                } else {
                    MSG("ERROR: coding rate setting is mandatory for implicit header mode\n");
                    return -1;
                }
            }

            MSG("INFO: Lora std channel> radio %i, IF %i Hz, %u Hz bw, SF %u, %s\n",
                    ifconf.rf_chain, ifconf.freq_hz, bw, sf,
                    (ifconf.implicit_hdr == true) ? "Implicit header" : "Explicit header");
        }
        if (lgw_rxif_setconf(8, &ifconf) != LGW_HAL_SUCCESS) {
            MSG("ERROR: invalid configuration for Lora standard channel\n");
            return -1;
        }
    }

    /* set configuration for FSK channel */
    memset(&ifconf, 0, sizeof ifconf); /* initialize configuration structure */
    val = json_object_get_value(conf_obj, "chan_FSK"); /* fetch value (if possible) */
    if (json_value_get_type(val) != JSONObject) {
        MSG("INFO: no configuration for FSK channel\n");
    } else {
        val = json_object_dotget_value(conf_obj, "chan_FSK.enable");
        if (json_value_get_type(val) == JSONBoolean) {
            ifconf.enable = (bool)json_value_get_boolean(val);
        } else {
            ifconf.enable = false;
        }
        if (ifconf.enable == false) {
            MSG("INFO: FSK channel %i disabled\n", i);
        } else  {
            ifconf.rf_chain = (unsigned int)json_object_dotget_number(conf_obj, "chan_FSK.radio");
            ifconf.freq_hz = (int32_t)json_object_dotget_number(conf_obj, "chan_FSK.if");
            bw = (unsigned int)json_object_dotget_number(conf_obj, "chan_FSK.bandwidth");
            fdev = (unsigned int)json_object_dotget_number(conf_obj, "chan_FSK.freq_deviation");
            ifconf.datarate = (unsigned int)json_object_dotget_number(conf_obj, "chan_FSK.datarate");

            /* if chan_FSK.bandwidth is set, it has priority over chan_FSK.freq_deviation */
            if ((bw == 0) && (fdev != 0)) {
                bw = 2 * fdev + ifconf.datarate;
            }
            if      (bw == 0)      ifconf.bandwidth = BW_UNDEFINED;
#if 0 /* TODO */
            else if (bw <= 7800)   ifconf.bandwidth = BW_7K8HZ;
            else if (bw <= 15600)  ifconf.bandwidth = BW_15K6HZ;
            else if (bw <= 31200)  ifconf.bandwidth = BW_31K2HZ;
            else if (bw <= 62500)  ifconf.bandwidth = BW_62K5HZ;
#endif
            else if (bw <= 125000) ifconf.bandwidth = BW_125KHZ;
            else if (bw <= 250000) ifconf.bandwidth = BW_250KHZ;
            else if (bw <= 500000) ifconf.bandwidth = BW_500KHZ;
            else ifconf.bandwidth = BW_UNDEFINED;

            MSG("INFO: FSK channel> radio %i, IF %i Hz, %u Hz bw, %u bps datarate\n",
                    ifconf.rf_chain, ifconf.freq_hz, bw, ifconf.datarate);
        }
        if (lgw_rxif_setconf(9, &ifconf) != LGW_HAL_SUCCESS) {
            MSG("ERROR: invalid configuration for FSK channel\n");
            return -1;
        }
    }
    json_value_free(root_val);

    return 0;
}

static int parse_gateway_configuration(const char * conf_array) {
    const char conf_obj_name[] = "gateway_conf";
    JSON_Value *root_val;
    JSON_Object *conf_obj = NULL;
    JSON_Value *val = NULL; /* needed to detect the absence of some fields */
    const char *str; /* pointer to sub-strings in the JSON data */
    unsigned long long ull = 0;

    /* try to parse JSON */
    root_val = json_parse_array_with_comments(conf_array);
    if (root_val == NULL) {
        MSG("ERROR: conf array is not a valid JSON string\n");
        exit(EXIT_FAILURE);
    }

    /* point to the gateway configuration object */
    conf_obj = json_object_get_object(json_value_get_object(root_val), conf_obj_name);
    if (conf_obj == NULL) {
        MSG("INFO: conf array does not contain a JSON object named %s\n", conf_obj_name);
        return -1;
    } else {
        MSG("INFO: conf array does contain a JSON object named %s, parsing gateway parameters\n", conf_obj_name);
    }

    /* gateway unique identifier (aka MAC address) (optional) */
    str = json_object_get_string(conf_obj, "gateway_ID");
    if (str != NULL) {
        sscanf(str, "%llx", &ull);
        lgwm = ull;
        MSG("INFO: gateway MAC address is configured to %016llX\n", ull);
    }

    /* server hostname or IP address (optional) */
    str = json_object_get_string(conf_obj, "server_address");
    if (str != NULL) {
        strncpy(serv_addr, str, sizeof serv_addr);
        serv_addr[sizeof serv_addr - 1] = '\0'; /* ensure string termination */
        MSG("INFO: server hostname or IP address is configured to \"%s\"\n", serv_addr);
    }

    /* get up and down ports (optional) */
    val = json_object_get_value(conf_obj, "serv_port_up");
    if (val != NULL) {
        snprintf(serv_port_up, sizeof serv_port_up, "%u", (uint16_t)json_value_get_number(val));
        MSG("INFO: upstream port is configured to \"%s\"\n", serv_port_up);
    }
    val = json_object_get_value(conf_obj, "serv_port_down");
    if (val != NULL) {
        snprintf(serv_port_down, sizeof serv_port_down, "%u", (uint16_t)json_value_get_number(val));
        MSG("INFO: downstream port is configured to \"%s\"\n", serv_port_down);
    }

    /* get keep-alive interval (in seconds) for downstream (optional) */
    val = json_object_get_value(conf_obj, "keepalive_interval");
    if (val != NULL) {
        keepalive_time = (int)json_value_get_number(val);
        MSG("INFO: downstream keep-alive interval is configured to %u seconds\n", keepalive_time);
    }

    /* get interval (in seconds) for statistics display (optional) */
    val = json_object_get_value(conf_obj, "stat_interval");
    if (val != NULL) {
        stat_interval = (unsigned)json_value_get_number(val);
        MSG("INFO: statistics display interval is configured to %u seconds\n", stat_interval);
    }

    /* get time-out value (in ms) for upstream datagrams (optional) */
    val = json_object_get_value(conf_obj, "push_timeout_ms");
    if (val != NULL) {
        push_timeout_half.tv_usec = 500 * (long int)json_value_get_number(val);
        MSG("INFO: upstream PUSH_DATA time-out is configured to %u ms\n", (unsigned)(push_timeout_half.tv_usec / 500));
    }

    /* packet filtering parameters */
    val = json_object_get_value(conf_obj, "forward_crc_valid");
    if (json_value_get_type(val) == JSONBoolean) {
        fwd_valid_pkt = (bool)json_value_get_boolean(val);
    }
    MSG("INFO: packets received with a valid CRC will%s be forwarded\n", (fwd_valid_pkt ? "" : " NOT"));
    val = json_object_get_value(conf_obj, "forward_crc_error");
    if (json_value_get_type(val) == JSONBoolean) {
        fwd_error_pkt = (bool)json_value_get_boolean(val);
    }
    MSG("INFO: packets received with a CRC error will%s be forwarded\n", (fwd_error_pkt ? "" : " NOT"));
    val = json_object_get_value(conf_obj, "forward_crc_disabled");
    if (json_value_get_type(val) == JSONBoolean) {
        fwd_nocrc_pkt = (bool)json_value_get_boolean(val);
    }
    MSG("INFO: packets received with no CRC will%s be forwarded\n", (fwd_nocrc_pkt ? "" : " NOT"));

    /* get reference coordinates */
    val = json_object_get_value(conf_obj, "ref_latitude");
    if (val != NULL) {
        reference_coord.lat = (double)json_value_get_number(val);
        MSG("INFO: Reference latitude is configured to %f deg\n", reference_coord.lat);
    }
    val = json_object_get_value(conf_obj, "ref_longitude");
    if (val != NULL) {
        reference_coord.lon = (double)json_value_get_number(val);
        MSG("INFO: Reference longitude is configured to %f deg\n", reference_coord.lon);
    }
    val = json_object_get_value(conf_obj, "ref_altitude");
    if (val != NULL) {
        reference_coord.alt = (short)json_value_get_number(val);
        MSG("INFO: Reference altitude is configured to %i meters\n", reference_coord.alt);
    }

    /* Gateway GPS coordinates hardcoding (aka. faking) option */
    val = json_object_get_value(conf_obj, "fake_gps");
    if (json_value_get_type(val) == JSONBoolean) {
        gps_fake_enable = (bool)json_value_get_boolean(val);
        if (gps_fake_enable == true) {
            MSG("INFO: fake GPS is enabled\n");
        } else {
            MSG("INFO: fake GPS is disabled\n");
        }
    }

    /* Beacon signal period (optional) */
    val = json_object_get_value(conf_obj, "beacon_period");
    if (val != NULL) {
        beacon_period = (unsigned int)json_value_get_number(val);
        if ((beacon_period > 0) && (beacon_period < 6)) {
            MSG("ERROR: invalid configuration for Beacon period, must be >= 6s\n");
            return -1;
        } else {
            MSG("INFO: Beaconing period is configured to %u seconds\n", beacon_period);
        }
    }

    /* Beacon TX frequency (optional) */
    val = json_object_get_value(conf_obj, "beacon_freq_hz");
    if (val != NULL) {
        beacon_freq_hz = (unsigned int)json_value_get_number(val);
        MSG("INFO: Beaconing signal will be emitted at %u Hz\n", beacon_freq_hz);
    }

    /* Number of beacon channels (optional) */
    val = json_object_get_value(conf_obj, "beacon_freq_nb");
    if (val != NULL) {
        beacon_freq_nb = (uint8_t)json_value_get_number(val);
        MSG("INFO: Beaconing channel number is set to %u\n", beacon_freq_nb);
    }

    /* Frequency step between beacon channels (optional) */
    val = json_object_get_value(conf_obj, "beacon_freq_step");
    if (val != NULL) {
        beacon_freq_step = (unsigned int)json_value_get_number(val);
        MSG("INFO: Beaconing channel frequency step is set to %uHz\n", beacon_freq_step);
    }

    /* Beacon datarate (optional) */
    val = json_object_get_value(conf_obj, "beacon_datarate");
    if (val != NULL) {
        beacon_datarate = (uint8_t)json_value_get_number(val);
        MSG("INFO: Beaconing datarate is set to SF%d\n", beacon_datarate);
    }

    /* Beacon modulation bandwidth (optional) */
    val = json_object_get_value(conf_obj, "beacon_bw_hz");
    if (val != NULL) {
        beacon_bw_hz = (unsigned int)json_value_get_number(val);
        MSG("INFO: Beaconing modulation bandwidth is set to %dHz\n", beacon_bw_hz);
    }

    /* Beacon TX power (optional) */
    val = json_object_get_value(conf_obj, "beacon_power");
    if (val != NULL) {
        beacon_power = (int8_t)json_value_get_number(val);
        MSG("INFO: Beaconing TX power is set to %ddBm\n", beacon_power);
    }

    /* Beacon information descriptor (optional) */
    val = json_object_get_value(conf_obj, "beacon_infodesc");
    if (val != NULL) {
        beacon_infodesc = (uint8_t)json_value_get_number(val);
        MSG("INFO: Beaconing information descriptor is set to %u\n", beacon_infodesc);
    }

    /* Auto-quit threshold (optional) */
    val = json_object_get_value(conf_obj, "autoquit_threshold");
    if (val != NULL) {
        autoquit_threshold = (unsigned int)json_value_get_number(val);
        MSG("INFO: Auto-quit after %u non-acknowledged PULL_DATA\n", autoquit_threshold);
    }

    /* free JSON parsing data structure */
    json_value_free(root_val);
    return 0;
}

static int parse_debug_configuration(const char * config_array) {
    int i;
    const char conf_obj_name[] = "debug_conf";
    JSON_Value *root_val;
    JSON_Object *conf_obj = NULL;
    JSON_Array *conf_array = NULL;
    JSON_Object *conf_obj_array = NULL;
    const char *str; /* pointer to sub-strings in the JSON data */

    /* Initialize structure */
    memset(&debugconf, 0, sizeof debugconf);

    /* try to parse JSON */
    root_val = json_parse_array_with_comments(config_array);
    if (root_val == NULL) {
        MSG("ERROR: conf array is not a valid JSON string\n");
        exit(EXIT_FAILURE);
    }

    /* point to the gateway configuration object */
    conf_obj = json_object_get_object(json_value_get_object(root_val), conf_obj_name);
    if (conf_obj == NULL) {
        MSG("INFO: conf array does not contain a JSON object named %s\n", conf_obj_name);
        json_value_free(root_val);
        return -1;
    } else {
        MSG("INFO: conf array does contain a JSON object named %s, parsing debug parameters\n", conf_obj_name);
    }

    /* Get reference payload configuration */
    conf_array = json_object_get_array (conf_obj, "ref_payload");
    if (conf_array != NULL) {
        debugconf.nb_ref_payload = json_array_get_count(conf_array);
        MSG("INFO: got %u debug reference payload\n", debugconf.nb_ref_payload);

        for (i = 0; i < (int)debugconf.nb_ref_payload; i++) {
            conf_obj_array = json_array_get_object(conf_array, i);
            /* id */
            str = json_object_get_string(conf_obj_array, "id");
            if (str != NULL) {
                sscanf(str, "0x%08X", &(debugconf.ref_payload[i].id));
                MSG("INFO: reference payload ID %d is 0x%08X\n", i, debugconf.ref_payload[i].id);
            }

            /* global count */
            nb_pkt_received_ref[i] = 0;
        }
    }

    /* Commit configuration */
    if (lgw_debug_setconf(&debugconf) != LGW_HAL_SUCCESS) {
        MSG("ERROR: Failed to configure debug\n");
        json_value_free(root_val);
        return -1;
    }

    /* free JSON parsing data structure */
    json_value_free(root_val);
    return 0;
}

static uint16_t crc16(const uint8_t * data, unsigned size) {
    const uint16_t crc_poly = 0x1021;
    const uint16_t init_val = 0x0000;
    uint16_t x = init_val;
    unsigned i, j;

    if (data == NULL)  {
        return 0;
    }

    for (i=0; i<size; ++i) {
        x ^= (uint16_t)data[i] << 8;
        for (j=0; j<8; ++j) {
            x = (x & 0x8000) ? (x<<1) ^ crc_poly : (x<<1);
        }
    }

    return x;
}

static double difftimespec(struct timespec end, struct timespec beginning) {
    double x;

    x = 1E-9 * (double)(end.tv_nsec - beginning.tv_nsec);
    x += (double)(end.tv_sec - beginning.tv_sec);

    return x;
}

static int send_tx_ack(uint8_t token_h, uint8_t token_l, enum jit_error_e error, signed int error_value) {
    uint8_t buff_ack[ACK_BUFF_SIZE]; /* buffer to give feedback to server */
    int buff_index;
    int j;

    /* reset buffer */
    memset(&buff_ack, 0, sizeof buff_ack);

    /* Prepare downlink feedback to be sent to server */
    buff_ack[0] = PROTOCOL_VERSION;
    buff_ack[1] = token_h;
    buff_ack[2] = token_l;
    buff_ack[3] = PKT_TX_ACK;
    *(unsigned int *)(buff_ack + 4) = net_mac_h;
    *(unsigned int *)(buff_ack + 8) = net_mac_l;
    buff_index = 12; /* 12-byte header */

    /* Put no JSON string if there is nothing to report */
    if (error != JIT_ERROR_OK) {
        /* start of JSON structure */
        memcpy((void *)(buff_ack + buff_index), (void *)"{\"txpk_ack\":{", 13);
        buff_index += 13;
        /* set downlink error/warning status in JSON structure */
        switch( error ) {
            case JIT_ERROR_TX_POWER:
                memcpy((void *)(buff_ack + buff_index), (void *)"\"warn\":", 7);
                buff_index += 7;
                break;
            default:
                memcpy((void *)(buff_ack + buff_index), (void *)"\"error\":", 8);
                buff_index += 8;
                break;
        }
        /* set error/warning type in JSON structure */
        switch (error) {
            case JIT_ERROR_FULL:
            case JIT_ERROR_COLLISION_PACKET:
                memcpy((void *)(buff_ack + buff_index), (void *)"\"COLLISION_PACKET\"", 18);
                buff_index += 18;
                /* update stats */
                xSemaphoreTake(mx_meas_dw, portMAX_DELAY);
                meas_nb_tx_rejected_collision_packet += 1;
                xSemaphoreGive(mx_meas_dw);
                break;
            case JIT_ERROR_TOO_LATE:
                memcpy((void *)(buff_ack + buff_index), (void *)"\"TOO_LATE\"", 10);
                buff_index += 10;
                /* update stats */
                xSemaphoreTake(mx_meas_dw, portMAX_DELAY);
                meas_nb_tx_rejected_too_late += 1;
                xSemaphoreGive(mx_meas_dw);
                break;
            case JIT_ERROR_TOO_EARLY:
                memcpy((void *)(buff_ack + buff_index), (void *)"\"TOO_EARLY\"", 11);
                buff_index += 11;
                /* update stats */
                xSemaphoreTake(mx_meas_dw, portMAX_DELAY);
                meas_nb_tx_rejected_too_early += 1;
                xSemaphoreGive(mx_meas_dw);
                break;
            case JIT_ERROR_COLLISION_BEACON:
                memcpy((void *)(buff_ack + buff_index), (void *)"\"COLLISION_BEACON\"", 18);
                buff_index += 18;
                /* update stats */
                xSemaphoreTake(mx_meas_dw, portMAX_DELAY);
                meas_nb_tx_rejected_collision_beacon += 1;
                xSemaphoreGive(mx_meas_dw);
                break;
            case JIT_ERROR_TX_FREQ:
                memcpy((void *)(buff_ack + buff_index), (void *)"\"TX_FREQ\"", 9);
                buff_index += 9;
                break;
            case JIT_ERROR_TX_POWER:
                memcpy((void *)(buff_ack + buff_index), (void *)"\"TX_POWER\"", 10);
                buff_index += 10;
                break;
            case JIT_ERROR_GPS_UNLOCKED:
                memcpy((void *)(buff_ack + buff_index), (void *)"\"GPS_UNLOCKED\"", 14);
                buff_index += 14;
                break;
            default:
                memcpy((void *)(buff_ack + buff_index), (void *)"\"UNKNOWN\"", 9);
                buff_index += 9;
                break;
        }
        /* set error/warning details in JSON structure */
        switch (error) {
            case JIT_ERROR_TX_POWER:
                j = snprintf((char *)(buff_ack + buff_index), ACK_BUFF_SIZE-buff_index, ",\"value\":%d", error_value);
                if (j > 0) {
                    buff_index += j;
                } else {
                    MSG("ERROR: [up] snprintf failed line %u\n", (__LINE__ - 4));
                    exit(EXIT_FAILURE);
                }
                break;
            default:
                /* Do nothing */
                break;
        }
        /* end of JSON structure */
        memcpy((void *)(buff_ack + buff_index), (void *)"}}", 2);
        buff_index += 2;
    }

    buff_ack[buff_index] = 0; /* add string terminator, for safety */

    /* send datagram to server */
    //return send(sock_down, (void *)buff_ack, buff_index, 0);
    return sendto(sock_down, (void *)buff_ack, buff_index, 0, (struct sockaddr *)&dest_addr, sizeof(dest_addr));
}

static int dns_loopup(char *hostname, char *ip)
{
    struct hostent *he;
    struct in_addr **addrlist;

    if((he = gethostbyname(hostname)) == NULL){
        return -1;
    }

    addrlist = (struct in_addr **) he->h_addr_list;
    for(int i=0; addrlist[i] != NULL; i++){
        strncpy(ip, inet_ntoa(*addrlist[i]), IP_LEN);
        ip[IP_LEN-1] = '\0'; // just to be safe
        return 0;
    }

    return -1;
}

int pkt_fwd_main(void)
{
    int i; /* loop variable and temporary variable for return value */
    int x;
    int l, m;

    /* variables to get local copies of measurements */
    unsigned int cp_nb_rx_rcv;
    unsigned int cp_nb_rx_ok;
    unsigned int cp_nb_rx_bad;
    unsigned int cp_nb_rx_nocrc;
    unsigned int cp_up_pkt_fwd;
    unsigned int cp_up_network_byte;
    unsigned int cp_up_payload_byte;
    unsigned int cp_up_dgram_sent;
    unsigned int cp_up_ack_rcv;
    unsigned int cp_dw_pull_sent;
    unsigned int cp_dw_ack_rcv;
    unsigned int cp_dw_dgram_rcv;
    unsigned int cp_dw_network_byte;
    unsigned int cp_dw_payload_byte;
    unsigned int cp_nb_tx_ok;
    unsigned int cp_nb_tx_fail;
    unsigned int cp_nb_tx_requested = 0;
    unsigned int cp_nb_tx_rejected_collision_packet = 0;
    unsigned int cp_nb_tx_rejected_collision_beacon = 0;
    unsigned int cp_nb_tx_rejected_too_late = 0;
    unsigned int cp_nb_tx_rejected_too_early = 0;
    unsigned int cp_nb_beacon_queued = 0;
    unsigned int cp_nb_beacon_sent = 0;
    unsigned int cp_nb_beacon_rejected = 0;

    /* GPS coordinates variables */
    bool coord_ok = false;
    struct coord_s cp_gps_coord = {0.0, 0.0, 0};

    /* SX1302 data variables */
    unsigned int trig_tstamp;
    unsigned int inst_tstamp;
    float temperature;

    /* statistics variable */
    time_t t;
    char stat_timestamp[24];
    float rx_ok_ratio;
    float rx_bad_ratio;
    float rx_nocrc_ratio;
    float up_ack_ratio;
    float dw_ack_ratio;

    // init all mutexes
    mx_concent = xSemaphoreCreateMutex();
    assert(mx_concent);
    mx_xcorr = xSemaphoreCreateMutex();
    assert(mx_xcorr);
    mx_timeref = xSemaphoreCreateMutex();
    assert(mx_timeref);
    mx_meas_up = xSemaphoreCreateMutex();
    assert(mx_meas_up);
    mx_meas_dw = xSemaphoreCreateMutex();
    assert(mx_meas_dw);
    mx_meas_gps = xSemaphoreCreateMutex();
    assert(mx_meas_gps);
    mx_stat_rep = xSemaphoreCreateMutex();
    assert(mx_stat_rep);


    /* display version informations */
    MSG("*** Packet Forwarder ***\nVersion: " VERSION_STRING "\n");
    MSG("*** SX1302 HAL library version info ***\n%s\n***\n", lgw_version_info());

    /* display host endianness */
    #if __BYTE_ORDER__ == __ORDER_LITTLE_ENDIAN__
        MSG("INFO: Little endian host\n");
    #elif __BYTE_ORDER__ == __ORDER_BIG_ENDIAN__
        MSG("INFO: Big endian host\n");
    #else
        MSG("INFO: Host endianness unknown\n");
    #endif

    // pointer to array defined in global_conf.h (default: cn470)
    char *conf_array = NULL;

    // change conf_array if set to a different region
    if(config[FREQ_REGION].val != NULL){
        if(strncmp(config[FREQ_REGION].val, "eu868", 5) == 0){
            conf_array = malloc(sizeof(global_eu_conf));
            memcpy(conf_array, global_eu_conf, sizeof(global_eu_conf));
        } else if(strncmp(config[FREQ_REGION].val, "us915", 5) == 0){
            conf_array = malloc(sizeof(global_us_conf));
            memcpy(conf_array, global_us_conf, sizeof(global_us_conf));
        } else {
            conf_array = malloc(sizeof(global_cn_conf));
            memcpy(conf_array, global_cn_conf, sizeof(global_cn_conf));
        }
    } else {
            conf_array = malloc(sizeof(global_cn_conf));
            memcpy(conf_array, global_cn_conf, sizeof(global_cn_conf));
    }

    MSG("Config loaded into memory\n");

    // update radio_0 and radio_1 frequencies
    int fwd_offset = 8;  // forward '"freq": ' which is 8 characters.
    int new_freq_len = 9;  // sub-G with unit 'Hz' should have 9 characters
    char *radio0_index = strstr(conf_array, "\"freq\"");
    char *radio1_index = strstr(radio0_index + fwd_offset, "\"freq\"");

    if(config[FREQ_RADIO0].val != NULL && radio0_index != NULL){
        if(config[FREQ_RADIO0].len == new_freq_len)  // need to match the exact length
            strncpy(radio0_index + fwd_offset, config[FREQ_RADIO0].val, new_freq_len);
    }
    if(config[FREQ_RADIO1].val != NULL && radio1_index != NULL){
        if(config[FREQ_RADIO1].len == new_freq_len)  // need to match the exact length
            strncpy(radio1_index + fwd_offset, config[FREQ_RADIO1].val, new_freq_len);
    }

    /* load configuration files */
    x = parse_SX130x_configuration(conf_array);
    if (x != 0) {
        MSG("INFO: no SX130x configuration\n");
        exit(EXIT_FAILURE);
    }
    x = parse_gateway_configuration(conf_array);
    if (x != 0) {
        MSG("INFO: no gateway configuration\n");
        exit(EXIT_FAILURE);
    }
    x = parse_debug_configuration(conf_array);
    if (x != 0) {
        MSG("INFO: no debug configuration\n");
    }

    free(conf_array);

    // TODO
    /* Start GPS a.s.a.p., to allow it to lock */
    gps_enabled = false;
    gps_ref_valid = false;

#ifndef GPS_DISABLE
    i = lgw_gps_enable("ATGM336H", 0, gps_uart_num); /* HAL only verified with ATGM336H */
    if (i != LGW_GPS_SUCCESS) {
        printf("WARNING: [main] enable GPS failed\n");
        gps_enabled = false;
        gps_ref_valid = false;
    } else {
        printf("INFO: [main] enable GPS succeeded\n");
        gps_enabled = true;
        gps_ref_valid = false;
    }
#endif

    /* get timezone info */
    tzset();

    /* sanity check on configuration variables */
    // TODO

    // some debug to see if everything goes all right
    ESP_LOGI(PKT_TAG, "serv_addr: %s", serv_addr);
    ESP_LOGI(PKT_TAG, "serv_port_up: %s", serv_port_up);
    ESP_LOGI(PKT_TAG, "serv_port_down: %s", serv_port_down);
    ESP_LOGI(PKT_TAG, "udp_host: %s", udp_host);
    ESP_LOGI(PKT_TAG, "udp_port: %d", udp_port);
    ESP_LOGI(PKT_TAG, "gw_id: %s", gw_id);

    // use the values from json file if not set in config[]
    if(udp_host[0] == '\0'){
        strncpy(udp_host, serv_addr, sizeof udp_host);
        udp_host[sizeof udp_host - 1] = '\0'; /* ensure string termination */
    }
    if(udp_port == 0)
        udp_port = atoi(serv_port_up);

    unsigned long long ull = 0;
    if (gw_id[0] != '\0') {
        sscanf(gw_id, "%llx", &ull);
        lgwm = ull;
        MSG("INFO: gateway MAC address is configured to %016llX\n", ull);
    }

    /* process some of the configuration variables */
    net_mac_h = htonl((unsigned int)(0xFFFFFFFF & (lgwm>>32)));
    net_mac_l = htonl((unsigned int)(0xFFFFFFFF &  lgwm  ));

    // -------------------------------
    int addr_family = 0;
    int ip_protocol = 0;
    char ip[IP_LEN] = { 0 };

    addr_family = AF_INET;
    ip_protocol = IPPROTO_IP;
    sock_up = socket(addr_family, SOCK_DGRAM, ip_protocol);
    if (sock_up < 0) {
        ESP_LOGE(PKT_TAG, "Unable to create up socket: errno %d", errno);
        return -1;
    }
    sock_down = socket(addr_family, SOCK_DGRAM, ip_protocol);
    if (sock_down < 0) {
        ESP_LOGE(PKT_TAG, "Unable to create down socket: errno %d", errno);
        return -1;
    }
    ESP_LOGI(PKT_TAG, "Socket created, sending to %s:%d", udp_host, udp_port);

    dns_loopup(udp_host, ip);
    dest_addr.sin_addr.s_addr = inet_addr(ip);
    dest_addr.sin_family = AF_INET;
    dest_addr.sin_port = htons(udp_port);

    Init_Led(); // Initialize LED

#if 0
    /* network socket creation */
    struct addrinfo *result; /* store result of getaddrinfo */
    struct addrinfo *q; /* pointer to move into *result data */

    /* connect so we can send/receive packet with the server only */
    i = connect(sock_up, q->ai_addr, q->ai_addrlen);
    if (i != 0) {
        MSG("ERROR: [up] connect returned %s\n", strerror(errno));
        exit(EXIT_FAILURE);
    }
    freeaddrinfo(result);

    /* connect so we can send/receive packet with the server only */
    i = connect(sock_down, q->ai_addr, q->ai_addrlen);
    if (i != 0) {
        MSG("ERROR: [down] connect returned %s\n", strerror(errno));
        exit(EXIT_FAILURE);
    }
    freeaddrinfo(result);
#endif

    /* set upstream socket RX timeout */
    i = setsockopt(sock_up, SOL_SOCKET, SO_RCVTIMEO, (void *)&push_timeout_half, sizeof push_timeout_half);
    if (i != 0) {
        MSG("ERROR: [up] setsockopt returned %s\n", strerror(errno));
        exit(EXIT_FAILURE);
    }

    if (com_type == LGW_COM_SPI) {
        /* Board reset */
        lgw_reset();
    }

    for (l = 0; l < LGW_IF_CHAIN_NB; l++) {
        for (m = 0; m < 8; m++) {
            nb_pkt_log[l][m] = 0;
        }
    }

    /* starting the concentrator */
    i = lgw_start();
    if (i == LGW_HAL_SUCCESS) {
        MSG("INFO: [main] concentrator started, packet can now be received\n");
    } else {
        MSG("ERROR: [main] failed to start the concentrator\n");
        exit(EXIT_FAILURE);
    }

#if 0  // TODO
    /* get the concentrator EUI */
    uint64_t eui;
    i = lgw_get_eui(&eui);
    if (i != LGW_HAL_SUCCESS) {
        printf("ERROR: failed to get concentrator EUI\n");
    } else {
        printf("INFO: concentrator EUI: 0x%016" PRIx64 "\n", eui);
    }
#endif

    if( xTaskCreatePinnedToCore(((TaskFunction_t) vDaemonLedIndication), "led_flash", 4096, (void *)pLed, 1, NULL, tskNO_AFFINITY) == errCOULD_NOT_ALLOCATE_REQUIRED_MEMORY) {
        printf( "Failed to spawn led_flash\n");
    } else {
        printf( "led_flash spawned\n" );
    }

    /* JIT queue initialization */
    jit_queue_init(&jit_queue[0]);
    jit_queue_init(&jit_queue[1]);

    if( xTaskCreatePinnedToCore(((TaskFunction_t) thread_up), "thread_up", (4096*4), NULL, 6, &pThreadUp, tskNO_AFFINITY) == errCOULD_NOT_ALLOCATE_REQUIRED_MEMORY) {
        printf( "Failed to spawn thread_up\n");
        printf( "largest_free_block: %d\n", heap_caps_get_largest_free_block( MALLOC_CAP_INTERNAL | MALLOC_CAP_8BIT ));
    } else {
        printf( "Thread_up spawned\n" );
    }

    if( xTaskCreatePinnedToCore(((TaskFunction_t) thread_down), "thread_down", 4096*2, NULL, 6, NULL, tskNO_AFFINITY) == errCOULD_NOT_ALLOCATE_REQUIRED_MEMORY) {
        printf( "Failed to spawn thread_down\n");
    } else {
        printf( "Thread_down spawned\n" );
    }

    if( xTaskCreatePinnedToCore(((TaskFunction_t) thread_jit), "thread_jit", 4096*2, (void *)pJit, 6, NULL, tskNO_AFFINITY) == errCOULD_NOT_ALLOCATE_REQUIRED_MEMORY) {
        printf( "Failed to spawn thread_jit\n");
    } else {
        printf( "Thread_jit spawned\n" );
    }

    // update NS info on screen
    snprintf(out_info, sizeof out_info, "NS=%s:%d", (char *)udp_host, udp_port);
    if(strlen(udp_host) > 16)  // too long to put in a single line with ":port"
        snprintf(out_info + 13, 9, "...:%d", udp_port);
    out_info[22] = '\0';
    oled_show_one_line(0, 5, out_info, 1);

    /* spawn thread to manage GPS */
    if (gps_enabled == true) {
        printf( "spawn thread_gps...\n");
        xTaskCreate((TaskFunction_t) thread_gps, "thread_gps", 4096, (void *)gps_handle, 6, NULL);

        printf( "spawn thread_valid...\n");
        xTaskCreate((TaskFunction_t) thread_valid, "thread_valid", 4096, (void *)valid_handle, 6, NULL);
    }

    /* main loop task: statistics collection */
    while (!exit_sig && !quit_sig) {
        time_count = 0;
        while(time_count < stat_interval) {
            /* wait for next reporting interval */
            //wait_ms(1000 * stat_interval);
            vTaskDelay(1000 * TIME_REFRESH / portTICK_PERIOD_MS);
            time_count += TIME_REFRESH;

            /* get timestamp for statistics */
            t = time(NULL);
            // we use "Z" to replace the "GMT" to shorten the display
            strftime(stat_timestamp, sizeof stat_timestamp, "%F %T Z", gmtime(&t));
            if(wifi_ready == true)  // only update time if wifi is ready
                oled_show_one_line(0, 6, stat_timestamp, 1);
        }
        strftime(stat_timestamp, sizeof stat_timestamp, "%F %T %Z", gmtime(&t));

        /* access upstream statistics, copy and reset them */
        xSemaphoreTake(mx_meas_up, portMAX_DELAY);
        cp_nb_rx_rcv       = meas_nb_rx_rcv;
        cp_nb_rx_ok        = meas_nb_rx_ok;
        cp_nb_rx_bad       = meas_nb_rx_bad;
        cp_nb_rx_nocrc     = meas_nb_rx_nocrc;
        cp_up_pkt_fwd      = meas_up_pkt_fwd;
        cp_up_network_byte = meas_up_network_byte;
        cp_up_payload_byte = meas_up_payload_byte;
        cp_up_dgram_sent   = meas_up_dgram_sent;
        cp_up_ack_rcv      = meas_up_ack_rcv;
        meas_nb_rx_rcv = 0;
        meas_nb_rx_ok = 0;
        meas_nb_rx_bad = 0;
        meas_nb_rx_nocrc = 0;
        meas_up_pkt_fwd = 0;
        meas_up_network_byte = 0;
        meas_up_payload_byte = 0;
        meas_up_dgram_sent = 0;
        meas_up_ack_rcv = 0;
        xSemaphoreGive(mx_meas_up);
        if (cp_nb_rx_rcv > 0) {
            rx_ok_ratio = (float)cp_nb_rx_ok / (float)cp_nb_rx_rcv;
            rx_bad_ratio = (float)cp_nb_rx_bad / (float)cp_nb_rx_rcv;
            rx_nocrc_ratio = (float)cp_nb_rx_nocrc / (float)cp_nb_rx_rcv;
        } else {
            rx_ok_ratio = 0.0;
            rx_bad_ratio = 0.0;
            rx_nocrc_ratio = 0.0;
        }
        if (cp_up_dgram_sent > 0) {
            up_ack_ratio = (float)cp_up_ack_rcv / (float)cp_up_dgram_sent;
        } else {
            up_ack_ratio = 0.0;
        }

        /* access downstream statistics, copy and reset them */
        xSemaphoreTake(mx_meas_dw, portMAX_DELAY);
        cp_dw_pull_sent    =  meas_dw_pull_sent;
        cp_dw_ack_rcv      =  meas_dw_ack_rcv;
        cp_dw_dgram_rcv    =  meas_dw_dgram_rcv;
        cp_dw_network_byte =  meas_dw_network_byte;
        cp_dw_payload_byte =  meas_dw_payload_byte;
        cp_nb_tx_ok        =  meas_nb_tx_ok;
        cp_nb_tx_fail      =  meas_nb_tx_fail;
        cp_nb_tx_requested                 +=  meas_nb_tx_requested;
        cp_nb_tx_rejected_collision_packet +=  meas_nb_tx_rejected_collision_packet;
        cp_nb_tx_rejected_collision_beacon +=  meas_nb_tx_rejected_collision_beacon;
        cp_nb_tx_rejected_too_late         +=  meas_nb_tx_rejected_too_late;
        cp_nb_tx_rejected_too_early        +=  meas_nb_tx_rejected_too_early;
        cp_nb_beacon_queued   +=  meas_nb_beacon_queued;
        cp_nb_beacon_sent     +=  meas_nb_beacon_sent;
        cp_nb_beacon_rejected +=  meas_nb_beacon_rejected;
        meas_dw_pull_sent = 0;
        meas_dw_ack_rcv = 0;
        meas_dw_dgram_rcv = 0;
        meas_dw_network_byte = 0;
        meas_dw_payload_byte = 0;
        meas_nb_tx_ok = 0;
        meas_nb_tx_fail = 0;
        meas_nb_tx_requested = 0;
        meas_nb_tx_rejected_collision_packet = 0;
        meas_nb_tx_rejected_collision_beacon = 0;
        meas_nb_tx_rejected_too_late = 0;
        meas_nb_tx_rejected_too_early = 0;
        meas_nb_beacon_queued = 0;
        meas_nb_beacon_sent = 0;
        meas_nb_beacon_rejected = 0;
        xSemaphoreGive(mx_meas_dw);
        if (cp_dw_pull_sent > 0) {
            dw_ack_ratio = (float)cp_dw_ack_rcv / (float)cp_dw_pull_sent;
        } else {
            dw_ack_ratio = 0.0;
        }

        /* access GPS statistics, copy them */
        if (gps_enabled == true) {
            xSemaphoreTake(mx_meas_gps, portMAX_DELAY);
            coord_ok = gps_coord_valid;
            cp_gps_coord = meas_gps_coord;
            xSemaphoreGive(mx_meas_gps);
        }

        /* overwrite with reference coordinates if function is enabled */
        if (gps_fake_enable == true) {
            cp_gps_coord = reference_coord;
        }

        /* display a report */
        printf("\n##### %s #####\n", stat_timestamp);
        printf("### [UPSTREAM] ###\n");
        printf("# RF packets received by concentrator: %u\n", cp_nb_rx_rcv);
        printf("# CRC_OK: %.2f%%, CRC_FAIL: %.2f%%, NO_CRC: %.2f%%\n", 100.0 * rx_ok_ratio, 100.0 * rx_bad_ratio, 100.0 * rx_nocrc_ratio);
        printf("# RF packets forwarded: %u (%u bytes)\n", cp_up_pkt_fwd, cp_up_payload_byte);
        printf("# PUSH_DATA datagrams sent: %u (%u bytes)\n", cp_up_dgram_sent, cp_up_network_byte);
        printf("# PUSH_DATA acknowledged: %.2f%%\n", 100.0 * up_ack_ratio);
        printf("### [DOWNSTREAM] ###\n");
        printf("# PULL_DATA sent: %u (%.2f%% acknowledged)\n", cp_dw_pull_sent, 100.0 * dw_ack_ratio);
        printf("# PULL_RESP(onse) datagrams received: %u (%u bytes)\n", cp_dw_dgram_rcv, cp_dw_network_byte);
        printf("# RF packets sent to concentrator: %u (%u bytes)\n", (cp_nb_tx_ok+cp_nb_tx_fail), cp_dw_payload_byte);
        printf("# TX errors: %u\n", cp_nb_tx_fail);
        if (cp_nb_tx_requested != 0 ) {
            printf("# TX rejected (collision packet): %.2f%% (req:%u, rej:%u)\n", 100.0 * cp_nb_tx_rejected_collision_packet / cp_nb_tx_requested, cp_nb_tx_requested, cp_nb_tx_rejected_collision_packet);
            printf("# TX rejected (collision beacon): %.2f%% (req:%u, rej:%u)\n", 100.0 * cp_nb_tx_rejected_collision_beacon / cp_nb_tx_requested, cp_nb_tx_requested, cp_nb_tx_rejected_collision_beacon);
            printf("# TX rejected (too late): %.2f%% (req:%u, rej:%u)\n", 100.0 * cp_nb_tx_rejected_too_late / cp_nb_tx_requested, cp_nb_tx_requested, cp_nb_tx_rejected_too_late);
            printf("# TX rejected (too early): %.2f%% (req:%u, rej:%u)\n", 100.0 * cp_nb_tx_rejected_too_early / cp_nb_tx_requested, cp_nb_tx_requested, cp_nb_tx_rejected_too_early);
        }
        printf("### SX1302 Status ###\n");
        xSemaphoreTake(mx_concent, portMAX_DELAY);
        i  = lgw_get_instcnt(&inst_tstamp);
        i |= lgw_get_trigcnt(&trig_tstamp);
        xSemaphoreGive(mx_concent);
        if (i != LGW_HAL_SUCCESS) {
            printf("# SX1302 counter unknown\n");
        } else {
            printf("# SX1302 counter (INST): %u\n", inst_tstamp);
            printf("# SX1302 counter (PPS):  %u\n", trig_tstamp);
        }
        printf("# BEACON queued: %u\n", cp_nb_beacon_queued);
        printf("# BEACON sent so far: %u\n", cp_nb_beacon_sent);
        printf("# BEACON rejected: %u\n", cp_nb_beacon_rejected);
        printf("### [JIT] ###\n");
        /* get timestamp captured on PPM pulse  */
        jit_print_queue (&jit_queue[0], false, DEBUG_LOG);
        printf("#--------\n");
        jit_print_queue (&jit_queue[1], false, DEBUG_LOG);
        printf("### [GPS] ###\n");
        if (gps_enabled == true) {
            /* no need for mutex, display is not critical */
            if (gps_ref_valid == true) {
                printf("# Valid time reference (age: %li sec)\n", (long)difftime(time(NULL), time_reference_gps.systime));
            } else {
                printf("# Invalid time reference (age: %li sec)\n", (long)difftime(time(NULL), time_reference_gps.systime));
            }
            if (coord_ok == true) {
                printf("# GPS coordinates: latitude %.5f, longitude %.5f, altitude %i m\n", cp_gps_coord.lat, cp_gps_coord.lon, cp_gps_coord.alt);
            } else {
                printf("# no valid GPS coordinates available yet\n");
            }
        } else if (gps_fake_enable == true) {
            printf("# GPS *FAKE* coordinates: latitude %.5f, longitude %.5f, altitude %i m\n", cp_gps_coord.lat, cp_gps_coord.lon, cp_gps_coord.alt);
        } else {
            printf("# GPS sync is disabled\n");
        }
        xSemaphoreTake(mx_concent, portMAX_DELAY);
        i = lgw_get_temperature(&temperature);
        xSemaphoreGive(mx_concent);
        if (i != LGW_HAL_SUCCESS) {
            printf("### Concentrator temperature unknown ###\n");
        } else {
            printf("### Concentrator temperature: %.0f C ###\n", temperature);

            snprintf(out_info, 22, "Temp=%.1fC  GPS=(N/A)", temperature);
            if(wifi_ready == true)  // only update time if wifi is ready
                oled_show_one_line(0, 7, out_info, 1);
        }
        printf("##### END #####\n");

        /* generate a JSON report (will be sent to server by upstream thread) */
        xSemaphoreTake(mx_stat_rep, portMAX_DELAY);
        if (((gps_enabled == true) && (coord_ok == true)) || (gps_fake_enable == true)) {
            snprintf(status_report, STATUS_SIZE, "\"stat\":{\"time\":\"%s\",\"lati\":%.5f,\"long\":%.5f,\"alti\":%i,\"rxnb\":%u,\"rxok\":%u,\"rxfw\":%u,\"ackr\":%.1f,\"dwnb\":%u,\"txnb\":%u,\"temp\":%.1f}", stat_timestamp, cp_gps_coord.lat, cp_gps_coord.lon, cp_gps_coord.alt, cp_nb_rx_rcv, cp_nb_rx_ok, cp_up_pkt_fwd, 100.0 * up_ack_ratio, cp_dw_dgram_rcv, cp_nb_tx_ok, temperature);
        } else {
            snprintf(status_report, STATUS_SIZE, "\"stat\":{\"time\":\"%s\",\"rxnb\":%u,\"rxok\":%u,\"rxfw\":%u,\"ackr\":%.1f,\"dwnb\":%u,\"txnb\":%u,\"temp\":%.1f}", stat_timestamp, cp_nb_rx_rcv, cp_nb_rx_ok, cp_up_pkt_fwd, 100.0 * up_ack_ratio, cp_dw_dgram_rcv, cp_nb_tx_ok, temperature);
        }
        report_ready = true;
        xSemaphoreGive(mx_stat_rep);
    }

    // TODO
    /* wait for all threads with a COM with the concentrator board to finish (1 fetch cycle max) */
#if 0
    i = pthread_join(thrid_up, NULL);
    if (i != 0) {
        printf("ERROR: failed to join upstream thread with %d - %s\n", i, strerror(errno));
    }
    i = pthread_join(thrid_down, NULL);
    if (i != 0) {
        printf("ERROR: failed to join downstream thread with %d - %s\n", i, strerror(errno));
    }
    i = pthread_join(thrid_jit, NULL);
    if (i != 0) {
        printf("ERROR: failed to join JIT thread with %d - %s\n", i, strerror(errno));
    }
    if (spectral_scan_params.enable == true) {
        i = pthread_join(thrid_ss, NULL);
        if (i != 0) {
            printf("ERROR: failed to join Spectral Scan thread with %d - %s\n", i, strerror(errno));
        }
    }
    if (gps_enabled == true) {
        pthread_cancel(thrid_gps); /* don't wait for GPS thread, no access to concentrator board */
        pthread_cancel(thrid_valid); /* don't wait for validation thread, no access to concentrator board */

        i = lgw_gps_disable(gps_uart_num);
        if (i == LGW_HAL_SUCCESS) {
            MSG("INFO: GPS closed successfully\n");
        } else {
            MSG("WARNING: failed to close GPS successfully\n");
        }
    }

    /* if an exit signal was received, try to quit properly */
    if (exit_sig) {
        /* shut down network sockets */
        shutdown(sock_up, SHUT_RDWR);
        shutdown(sock_down, SHUT_RDWR);
        /* stop the hardware */
        i = lgw_stop();
        if (i == LGW_HAL_SUCCESS) {
            MSG("INFO: concentrator stopped successfully\n");
        } else {
            MSG("WARNING: failed to stop concentrator successfully\n");
        }
    }
#endif

    if (com_type == LGW_COM_SPI) {
        /* Board reset */
        lgw_reset();
    }

    MSG("INFO: Exiting packet forwarder program\n");
    return 0;
}
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
void app_main(void)
{
    int reboot_delay_s;
    bool soft_ap_mode = false;

    printf("\n\n*** ESXP1302 Gateway. Version: %s ***\n\n\n", EXSP1302_VERSION);

    oled_init();
    oled_cls();
    oled_show_str(0, 0, "ESXP1302 GATEWAY", 2);
    sprintf(out_info,   "            (v%s)", EXSP1302_VERSION);
    oled_show_one_line(0, 2, out_info, 1);

    gpio_set_direction(USER_BUTTON_1, GPIO_MODE_INPUT);
    gpio_set_direction(USER_BUTTON_2, GPIO_MODE_INPUT);

    if(BUTTON_PRESSED == 0){
        gpio_pullup_en(USER_BUTTON_1);
        gpio_pullup_en(USER_BUTTON_2);
    } else {
        gpio_pulldown_en(USER_BUTTON_1);
        gpio_pulldown_en(USER_BUTTON_2);
    }

    read_config_from_nvs();

    if(gpio_get_level(USER_BUTTON_1) == BUTTON_PRESSED && USER_BUTTON_1 != GPIO_NUM_NC){
        printf("User button 1 is PRESSED, go to soft AP mode\n");
        soft_ap_mode = true;
    } else if(gpio_get_level(USER_BUTTON_2) == BUTTON_PRESSED && USER_BUTTON_2 != GPIO_NUM_NC){
        printf("User button 2 is PRESSED, go to station mode\n");
        soft_ap_mode = false;
    } else if(config[WIFI_MODE].val == NULL){
        soft_ap_mode = true;  // if not set yet, go to soft_ap mode as the default
    } else if(strncmp(config[WIFI_MODE].val, "soft_ap", 7) == 0){
        soft_ap_mode = true;
    }

    if(soft_ap_mode == true){
        config_wifi_mode(WIFI_MODE_STATION);

        // set up timer for reboot
        reboot_delay_s = 60 * 10; // 10 minutes
        reboot_flag = true;
        start_reboot_timer_ms(reboot_delay_s * 1000); // change to ms

        ESP_LOGI(BOOT_TAG, "ESP_WIFI_MODE_SOFT_AP");
        wifi_init_soft_ap();

        oled_show_one_line(0, 3, "IP=192.168.4.1", 2);
        oled_show_one_line(0, 5, "Soft AP mode", 1);

        sprintf(out_info, "SSID=%s", ESP_WIFI_SSID);
        oled_show_one_line(0, 6, out_info, 1);
        sprintf(out_info, "PSWD=%s", ESP_WIFI_PASS);
        oled_show_one_line(0, 7, out_info, 1);

    } else {
        oled_show_one_line(0, 3, "station mode", 1);

        oled_show_one_line(0, 4, "Wifi not connected.", 1);
        oled_show_str(0, 5, "You can re-config wifi at command line or under Soft-AP mode.  ", 1);

        // assume wifi can't connect; set up timer preparing for reboot soon
        config_wifi_mode(WIFI_MODE_SOFT_AP);
        reboot_delay_s = 60 * 5; // 5 minutes
        reboot_flag = true;
        start_reboot_timer_ms(reboot_delay_s * 1000); // change to ms

        ESP_LOGI(BOOT_TAG, "ESP_WIFI_MODE_STA");
        wifi_init_sta();
    }

    // start http service
    xTaskCreate(((TaskFunction_t) http_server_task), "http_server", 1*4096, NULL, 6, NULL);

    esp_rom_gpio_pad_select_gpio(BLINK_GPIO);
    gpio_set_direction(BLINK_GPIO,GPIO_MODE_OUTPUT);
    gpio_set_level(BLINK_GPIO, 1);

    // start command line
    esp_console_repl_config_t repl_config = ESP_CONSOLE_REPL_CONFIG_DEFAULT();
    repl_config.task_stack_size = 4096 * 2;
    repl_config.prompt = "ESXP1302_GW>";

    usage();
    register_config();

    // initialize console REPL environment
    esp_console_repl_t *repl = NULL;
    esp_console_dev_uart_config_t uart_config = ESP_CONSOLE_DEV_UART_CONFIG_DEFAULT();
    ESP_ERROR_CHECK(esp_console_new_repl_uart(&uart_config, &repl_config, &repl));
    ESP_ERROR_CHECK(esp_console_start_repl(repl));

    gpio_set_level(BLINK_GPIO, 0);
}
