lora-gateway/esxp1302/main/libloragw/loragw_usb.c

/*
 / _____)             _              | |
( (____  _____ ____ _| |_ _____  ____| |__
 \____ \| ___ |    (_   _) ___ |/ ___)  _ \
 _____) ) ____| | | || |_| ____( (___| | | |
(______/|_____)_|_|_| \__)_____)\____)_| |_|
  (C)2020 Semtech

Description:
    Host specific functions to address the LoRa concentrator registers through
    a USB interface.
    Single-byte read/write and burst read/write.

License: Revised BSD License, see LICENSE.TXT file include in the project
*/


/* -------------------------------------------------------------------------- */
/* --- DEPENDANCIES --------------------------------------------------------- */

#include <stdint.h>     /* C99 types */
#include <stdbool.h>    /* bool type */
#include <stdio.h>      /* printf fprintf */
#include <stdlib.h>     /* malloc free */
#include <unistd.h>     /* lseek, close */
#include <fcntl.h>      /* open */
#include <string.h>     /* strncmp */
#include <errno.h>      /* Error number definitions */
#include <termios.h>    /* POSIX terminal control definitions */

#include "loragw_com.h"
#include "loragw_usb.h"
//#include "loragw_mcu.h"
#include "loragw_aux.h"

/* -------------------------------------------------------------------------- */
/* --- PRIVATE MACROS ------------------------------------------------------- */

#define ARRAY_SIZE(a) (sizeof(a) / sizeof((a)[0]))
#if DEBUG_COM == 1
    #define DEBUG_MSG(str)                fprintf(stdout, str)
    #define DEBUG_PRINTF(fmt, args...)    fprintf(stdout, fmt, args)
    #define CHECK_NULL(a)                if(a==NULL){fprintf(stderr,"%s:%d: ERROR: NULL POINTER AS ARGUMENT\n", __FUNCTION__, __LINE__);return LGW_USB_ERROR;}
#else
    #define DEBUG_MSG(str)
    #define DEBUG_PRINTF(fmt, args...)
    #define CHECK_NULL(a)                if(a==NULL){return LGW_USB_ERROR;}
#endif

/* -------------------------------------------------------------------------- */
/* --- PRIVATE CONSTANTS ---------------------------------------------------- */

/* -------------------------------------------------------------------------- */
/* --- PRIVATE TYPES -------------------------------------------------------- */

/* -------------------------------------------------------------------------- */
/* --- PRIVATE VARIABLES  --------------------------------------------------- */

//static lgw_com_write_mode_t _lgw_write_mode = LGW_COM_WRITE_MODE_SINGLE;
//static uint8_t _lgw_spi_req_nb = 0;

/* -------------------------------------------------------------------------- */
/* --- PRIVATE FUNCTIONS DEFINITION ----------------------------------------- */

#if 0 // esxp1302 doesn't support USB interface
int set_interface_attribs_linux(int fd, int speed) {
    struct termios tty;

    memset(&tty, 0, sizeof tty);

    /* Get current attributes */
    if (tcgetattr(fd, &tty) != 0) {
        DEBUG_PRINTF("ERROR: tcgetattr failed with %d - %s", errno, strerror(errno));
        return LGW_USB_ERROR;
    }

    cfsetospeed(&tty, speed);
    cfsetispeed(&tty, speed);

    /* Control Modes */
    tty.c_cflag = (tty.c_cflag & ~CSIZE) | CS8; /* set 8-bit characters */
    tty.c_cflag |= CLOCAL;                      /* local connection, no modem control */
    tty.c_cflag |= CREAD;                       /* enable receiving characters */
    tty.c_cflag &= ~PARENB;                     /* no parity */
    tty.c_cflag &= ~CSTOPB;                     /* one stop bit */
    /* Input Modes */
    tty.c_iflag &= ~IGNBRK;
    tty.c_iflag &= ~(IXON | IXOFF | IXANY | ICRNL);
    /* Output Modes */
    tty.c_oflag &= ~IGNBRK;
    tty.c_oflag &= ~(IXON | IXOFF | IXANY | ICRNL);
    /* Local Modes */
    tty.c_lflag = 0;
    /* Settings for non-canonical mode */
    tty.c_cc[VMIN] = 0;                         /* non-blocking mode */
    tty.c_cc[VTIME] = 0;                        /* wait for (n * 0.1) seconds before returning */

    /* Set attributes */
    if (tcsetattr(fd, TCSANOW, &tty) != 0) {
        DEBUG_PRINTF("ERROR: tcsetattr failed with %d - %s", errno, strerror(errno));
        return LGW_USB_ERROR;
    }

    return LGW_USB_SUCCESS;
}

/* ~~~~~~~~~~~~~~~~~~~~~~~~~~~~~~~~ */

/* configure serial interface to be read blocking or not*/
int set_blocking_linux(int fd, bool blocking) {
    struct termios tty;

    memset(&tty, 0, sizeof tty);

    /* Get current attributes */
    if (tcgetattr(fd, &tty) != 0) {
        DEBUG_PRINTF("ERROR: tcgetattr failed with %d - %s", errno, strerror(errno));
        return LGW_USB_ERROR;
    }

    tty.c_cc[VMIN] = (blocking == true) ? 1 : 0;    /* set blocking or non-blocking mode */
    tty.c_cc[VTIME] = 1;                            /* wait for (n * 0.1) seconds before returning */

    /* Set attributes */
    if (tcsetattr(fd, TCSANOW, &tty) != 0) {
        DEBUG_PRINTF("ERROR: tcsetattr failed with %d - %s", errno, strerror(errno));
        return LGW_USB_ERROR;
    }

    return LGW_USB_SUCCESS;
}
#endif // esxp1302 doesn't support USB interface

/* -------------------------------------------------------------------------- */
/* --- PUBLIC FUNCTIONS DEFINITION ------------------------------------------ */

int lgw_usb_open(void **com_target_ptr)
{
#if 0 // esxp1302 doesn't support USB interface

    int *usb_device = NULL;
    char portname[50];
    int x;
    int fd;
    s_ping_info gw_info;
    s_status mcu_status;
    uint8_t data;
    ssize_t n;

    /*check input variables*/
    CHECK_NULL(com_target_ptr);

    usb_device = malloc(sizeof(int));
    if (usb_device == NULL) {
        DEBUG_MSG("ERROR : MALLOC FAIL\n");
        return LGW_USB_ERROR;
    }

    /* open tty port */
    sprintf(portname, "%s", com_path);
    fd = open(portname, O_RDWR | O_NOCTTY | O_SYNC);
    if (fd < 0) {
        printf("ERROR: failed to open COM port %s - %s\n", portname, strerror(errno));
    } else {
        printf("INFO: Configuring TTY\n");
        x = set_interface_attribs_linux(fd, B115200);
        if (x != 0) {
            printf("ERROR: failed to configure COM port %s\n", portname);
            free(usb_device);
            return LGW_USB_ERROR;
        }

        /* flush tty port before setting it as blocking */
        printf("INFO: Flushing TTY\n");
        do {
            n = read(fd, &data, 1);
            if (n > 0) {
                printf("NOTE: flushing serial port (0x%2X)\n", data);
            }
        } while (n > 0);

        /* set tty port blocking */
        printf("INFO: Setting TTY in blocking mode\n");
        x = set_blocking_linux(fd, true);
        if (x != 0) {
            printf("ERROR: failed to configure COM port %s\n", portname);
            free(usb_device);
            return LGW_USB_ERROR;
        }

        *usb_device = fd;
        *com_target_ptr = (void*)usb_device;

        /* Initialize pseudo-random generator for MCU request ID */
        srand(0);

        /* Check MCU version (ignore first char of the received version (release/debug) */
        printf("INFO: Connect to MCU\n");
        if (mcu_ping(fd, &gw_info) != 0) {
            printf("ERROR: failed to ping the concentrator MCU\n");
            return LGW_USB_ERROR;
        }
        if (strncmp(gw_info.version + 1, mcu_version_string, sizeof mcu_version_string) != 0) {
            printf("WARNING: MCU version mismatch (expected:%s, got:%s)\n", mcu_version_string, gw_info.version);
        }
        printf("INFO: Concentrator MCU version is %s\n", gw_info.version);

        /* Get MCU status */
        if (mcu_get_status(fd, &mcu_status) != 0) {
            printf("ERROR: failed to get status from the concentrator MCU\n");
            return LGW_USB_ERROR;
        }
        printf("INFO: MCU status: sys_time:%u temperature:%.1foC\n", mcu_status.system_time_ms, mcu_status.temperature);

        /* Reset SX1302 */
        x  = mcu_gpio_write(fd, 0, 1, 1); /*   set PA1 : POWER_EN */
        x |= mcu_gpio_write(fd, 0, 2, 1); /*   set PA2 : SX1302_RESET active */
        x |= mcu_gpio_write(fd, 0, 2, 0); /* unset PA2 : SX1302_RESET inactive */
        /* Reset SX1261 (LBT / Spectral Scan) */
        x |= mcu_gpio_write(fd, 0, 8, 0); /*   set PA8 : SX1261_NRESET active */
        x |= mcu_gpio_write(fd, 0, 8, 1); /* unset PA8 : SX1261_NRESET inactive */
        if (x != 0) {
            printf("ERROR: failed to reset SX1302\n");
            free(usb_device);
            return LGW_USB_ERROR;
        }

        return LGW_USB_SUCCESS;
    }

    free(usb_device);
    return LGW_USB_ERROR;
#endif

    return LGW_USB_SUCCESS;
}

/* ~~~~~~~~~~~~~~~~~~~~~~~~~~~~~~~~ */

/* SPI release */
int lgw_usb_close(void *com_target) {

#if 0 // esxp1302 doesn't support USB interface

    int usb_device;
    int x, err = LGW_USB_SUCCESS;

    /* check input variables */
    CHECK_NULL(com_target);

    usb_device = *(int *)com_target;

    /* Reset SX1302 before closing */
    x  = mcu_gpio_write(usb_device, 0, 1, 1); /*   set PA1 : POWER_EN */
    x |= mcu_gpio_write(usb_device, 0, 2, 1); /*   set PA2 : SX1302_RESET active */
    x |= mcu_gpio_write(usb_device, 0, 2, 0); /* unset PA2 : SX1302_RESET inactive */
    /* Reset SX1261 (LBT / Spectral Scan) */
    x |= mcu_gpio_write(usb_device, 0, 8, 0); /*   set PA8 : SX1261_NRESET active */
    x |= mcu_gpio_write(usb_device, 0, 8, 1); /* unset PA8 : SX1261_NRESET inactive */
    if (x != 0) {
        printf("ERROR: failed to reset SX1302\n");
        err = LGW_USB_ERROR;
    }

    /* close file & deallocate file descriptor */
    x = close(usb_device);
    free(com_target);
    if (x != 0) {
        printf("ERROR: failed to close USB file\n");
        err = LGW_USB_ERROR;
    }

    /* determine return code */
    if (err != 0) {
        printf("ERROR: USB PORT FAILED TO CLOSE\n");
        return LGW_USB_ERROR;
    } else {
        DEBUG_MSG("Note: USB port closed\n");
        return LGW_USB_SUCCESS;
    }
#endif

    return LGW_USB_SUCCESS;
}

/* ~~~~~~~~~~~~~~~~~~~~~~~~~~~~~~~~ */

/* Simple write */
int lgw_usb_w(void *com_target, uint8_t spi_mux_target, uint16_t address, uint8_t data) {
    return lgw_usb_wb(com_target, spi_mux_target, address, &data, 1);
}

/* ~~~~~~~~~~~~~~~~~~~~~~~~~~~~~~~~ */

/* Simple read */
int lgw_usb_r(void *com_target, uint8_t spi_mux_target, uint16_t address, uint8_t *data) {
    return lgw_usb_rb(com_target, spi_mux_target, address, data, 1);
}

/* ~~~~~~~~~~~~~~~~~~~~~~~~~~~~~~~~ */

/* Single Byte Read-Modify-Write */
int lgw_usb_rmw(void *com_target, uint16_t address, uint8_t offs, uint8_t leng, uint8_t data)
{
#if 0 // esxp1302 doesn't support USB interface
    int usb_device;
    uint8_t command_size = 6;
    uint8_t in_out_buf[command_size];
    int a = 0;

    /* check input variables */
    CHECK_NULL(com_target);

    usb_device = *(int *)com_target;

    DEBUG_PRINTF("==> RMW register @ 0x%04X, offs:%u leng:%u value:0x%02X\n", address, offs, leng, data);

    /* prepare frame to be sent */
    in_out_buf[0] = _lgw_spi_req_nb; /* Req ID */
    in_out_buf[1] = MCU_SPI_REQ_TYPE_READ_MODIFY_WRITE; /* Req type */
    in_out_buf[2] = (uint8_t)(address >> 8); /* Register address MSB */
    in_out_buf[3] = (uint8_t)(address >> 0); /* Register address LSB */
    in_out_buf[4] = ((1 << leng) - 1) << offs; /* Register bitmask */
    in_out_buf[5] = data << offs;

    if (_lgw_write_mode == LGW_COM_WRITE_MODE_BULK) {
        a = mcu_spi_store(in_out_buf, command_size);
        _lgw_spi_req_nb += 1;
    } else {
        a = mcu_spi_write(usb_device, in_out_buf, command_size);
    }

    /* determine return code */
    if (a != 0) {
        DEBUG_MSG("ERROR: USB WRITE FAILURE\n");
        return -1;
    } else {
        DEBUG_MSG("Note: USB write success\n");
        return 0;
    }
#endif

    return 0;
}

/* ~~~~~~~~~~~~~~~~~~~~~~~~~~~~~~~~ */

/* Burst (multiple-byte) write */
int lgw_usb_wb(void *com_target, uint8_t spi_mux_target, uint16_t address, const uint8_t *data, uint16_t size)
{
#if 0 // esxp1302 doesn't support USB interface
    int usb_device;
    uint16_t command_size = size + 8; /* 5 bytes: REQ metadata (MCU), 3 bytes: SPI header (SX1302) */
    uint8_t in_out_buf[command_size];
    int i;
    int a = 0;

    /* check input parameters */
    CHECK_NULL(com_target);
    CHECK_NULL(data);

    usb_device = *(int *)com_target;

    /* prepare command */
    /* Request metadata */
    in_out_buf[0] = _lgw_spi_req_nb; /* Req ID */
    in_out_buf[1] = MCU_SPI_REQ_TYPE_READ_WRITE; /* Req type */
    in_out_buf[2] = MCU_SPI_TARGET_SX1302; /* MCU -> SX1302 */
    in_out_buf[3] = (uint8_t)((size + 3) >> 8); /* payload size + spi_mux_target + address */
    in_out_buf[4] = (uint8_t)((size + 3) >> 0); /* payload size + spi_mux_target + address */
    /* RAW SPI frame */
    in_out_buf[5] = spi_mux_target; /* SX1302 -> RADIO_A or RADIO_B */
    in_out_buf[6] = 0x80 | ((address >> 8) & 0x7F);
    in_out_buf[7] =        ((address >> 0) & 0xFF);
    for (i = 0; i < size; i++) {
        in_out_buf[i + 8] = data[i];
    }

    if (_lgw_write_mode == LGW_COM_WRITE_MODE_BULK) {
        a = mcu_spi_store(in_out_buf, command_size);
        _lgw_spi_req_nb += 1;
    } else {
        a = mcu_spi_write(usb_device, in_out_buf, command_size);
    }

    /* determine return code */
    if (a != 0) {
        DEBUG_MSG("ERROR: USB WRITE BURST FAILURE\n");
        return -1;
    } else {
        DEBUG_MSG("Note: USB write burst success\n");
        return 0;
    }
#endif

    return 0;
}

/* ~~~~~~~~~~~~~~~~~~~~~~~~~~~~~~~~ */

/* Burst (multiple-byte) read */
int lgw_usb_rb(void *com_target, uint8_t spi_mux_target, uint16_t address, uint8_t *data, uint16_t size)
{
#if 0 // esxp1302 doesn't support USB interface
    int usb_device;
    uint16_t command_size = size + 9;  /* 5 bytes: REQ metadata (MCU), 3 bytes: SPI header (SX1302), 1 byte: dummy*/
    uint8_t in_out_buf[command_size];
    int i;
    int a = 0;

    /* check input parameters */
    CHECK_NULL(com_target);
    CHECK_NULL(data);

    usb_device = *(int *)com_target;

    /* prepare command */
    /* Request metadata */
    in_out_buf[0] = 0; /* Req ID */
    in_out_buf[1] = MCU_SPI_REQ_TYPE_READ_WRITE; /* Req type */
    in_out_buf[2] = MCU_SPI_TARGET_SX1302; /* MCU -> SX1302 */
    in_out_buf[3] = (uint8_t)((size + 4) >> 8); /* payload size + spi_mux_target + address + dummy byte */
    in_out_buf[4] = (uint8_t)((size + 4) >> 0); /* payload size + spi_mux_target + address + dummy byte */
    /* RAW SPI frame */
    in_out_buf[5] = spi_mux_target; /* SX1302 -> RADIO_A or RADIO_B */
    in_out_buf[6] = 0x00 | ((address >> 8) & 0x7F);
    in_out_buf[7] =        ((address >> 0) & 0xFF);
    in_out_buf[8] = 0x00; /* dummy byte */
    for (i = 0; i < size; i++) {
        in_out_buf[i + 9] = data[i];
    }

    if (_lgw_write_mode == LGW_COM_WRITE_MODE_BULK) {
        /* makes no sense to read in bulk mode, as we can't get the result */
        printf("ERROR: USB READ BURST FAILURE - bulk mode is enabled\n");
        return -1;
    } else {
        a = mcu_spi_write(usb_device, in_out_buf, command_size);
    }

    /* determine return code */
    if (a != 0) {
        DEBUG_MSG("ERROR: USB READ BURST FAILURE\n");
        return -1;
    } else {
        DEBUG_MSG("Note: USB read burst success\n");
        memcpy(data, in_out_buf + 9, size); /* remove the first bytes, keep only the payload */
        return 0;
    }
#endif

    return 0;
}

/* ~~~~~~~~~~~~~~~~~~~~~~~~~~~~~~~~ */

int lgw_usb_set_write_mode(lgw_com_write_mode_t write_mode) {
#if 0 // esxp1302 doesn't support USB interface
    if (write_mode >= LGW_COM_WRITE_MODE_UNKNOWN) {
        printf("ERROR: wrong write mode\n");
        return -1;
    }

    DEBUG_PRINTF("INFO: setting USB write mode to %s\n", (write_mode == LGW_COM_WRITE_MODE_SINGLE) ? "SINGLE" : "BULK");

    _lgw_write_mode = write_mode;
#endif

    return 0;
}

/* ~~~~~~~~~~~~~~~~~~~~~~~~~~~~~~~~ */

int lgw_usb_flush(void *com_target)
{
    int a = 0;

#if 0 // esxp1302 doesn't support USB interface
    /* Check input parameters */
    CHECK_NULL(com_target);
    if (_lgw_write_mode != LGW_COM_WRITE_MODE_BULK) {
        printf("ERROR: %s: cannot flush in single write mode\n", __FUNCTION__);
        return -1;
    }

    /* Restore single mode after flushing */
    _lgw_write_mode = LGW_COM_WRITE_MODE_SINGLE;

    if (_lgw_spi_req_nb == 0) {
        printf("INFO: no SPI request to flush\n");
        return 0;
    }

    int usb_device = *(int *)com_target;

    DEBUG_MSG("INFO: flushing USB write buffer\n");
    a = mcu_spi_flush(usb_device);
    if (a != 0) {
        printf("ERROR: Failed to flush USB write buffer\n");
    }

    /* reset the pending request number */
    _lgw_spi_req_nb = 0;
#endif

    return a;
}

/* ~~~~~~~~~~~~~~~~~~~~~~~~~~~~~~~~ */

uint16_t lgw_usb_chunk_size(void) {
    return (uint16_t)LGW_USB_BURST_CHUNK;
}

/* ~~~~~~~~~~~~~~~~~~~~~~~~~~~~~~~~ */

int lgw_usb_get_temperature(void *com_target, float * temperature)
{
#if 0 // esxp1302 doesn't support USB interface
    int usb_device;
    s_status mcu_status;

    /* check input parameters */
    CHECK_NULL(com_target);
    CHECK_NULL(temperature);

    usb_device = *(int *)com_target;

    if (mcu_get_status(usb_device, &mcu_status) != 0) {
        printf("ERROR: failed to get status from the concentrator MCU\n");
        return -1;
    }
    DEBUG_PRINTF("INFO: temperature:%.1foC\n", mcu_status.temperature);

    *temperature = mcu_status.temperature;
#endif

    return 0;
}

/* --- EOF ------------------------------------------------------------------ */
