lora-gateway/esxp1302/main/libloragw/loragw_hal.c

/*
 / _____)             _              | |
( (____  _____ ____ _| |_ _____  ____| |__
 \____ \| ___ |    (_   _) ___ |/ ___)  _ \
 _____) ) ____| | | || |_| ____( (___| | | |
(______/|_____)_|_|_| \__)_____)\____)_| |_|
  (C)2019 Semtech

Description:
    LoRa concentrator Hardware Abstraction Layer

License: Revised BSD License, see LICENSE.TXT file include in the project
*/


/* -------------------------------------------------------------------------- */
/* --- DEPENDANCIES --------------------------------------------------------- */

/* fix an issue between POSIX and C99 */
#if __STDC_VERSION__ >= 199901L
    #define _XOPEN_SOURCE 600
#else
    #define _XOPEN_SOURCE 500
#endif

#include <stdlib.h>     /* qsort_r */
#include <stdint.h>     /* C99 types */
#include <stdbool.h>    /* bool type */
#include <stdio.h>      /* printf fprintf */
#include <string.h>     /* memcpy */
#include <unistd.h>     /* symlink, unlink */
#include <inttypes.h>

#include "loragw_reg.h"
#include "loragw_hal.h"
#include "loragw_aux.h"
#include "loragw_com.h"
#include "loragw_i2c.h"
#include "loragw_lbt.h"
#include "loragw_sx1250.h"
#include "loragw_sx125x.h"
#include "loragw_sx1261.h"
#include "loragw_sx1302.h"
#include "loragw_sx1302_timestamp.h"
#include "loragw_stts751.h"
#include "loragw_ad5338r.h"
#include "loragw_debug.h"


/* -------------------------------------------------------------------------- */
/* --- PRIVATE MACROS ------------------------------------------------------- */

#define ARRAY_SIZE(a) (sizeof(a) / sizeof((a)[0]))
#if DEBUG_HAL == 1
    #define DEBUG_MSG(str)                fprintf(stdout, str)
    #define DEBUG_PRINTF(fmt, args...)    fprintf(stdout,"%s:%d: "fmt, __FUNCTION__, __LINE__, args)
    #define DEBUG_ARRAY(a,b,c)            for(a=0;a<b;++a) fprintf(stdout,"%x.",c[a]);fprintf(stdout,"end\n")
    #define CHECK_NULL(a)                 if(a==NULL){fprintf(stderr,"%s:%d: ERROR: NULL POINTER AS ARGUMENT\n", __FUNCTION__, __LINE__);return LGW_HAL_ERROR;}
#else
    #define DEBUG_MSG(str)
    #define DEBUG_PRINTF(fmt, args...)
    #define DEBUG_ARRAY(a,b,c)            for(a=0;a!=0;){}
    #define CHECK_NULL(a)                 if(a==NULL){return LGW_HAL_ERROR;}
#endif

#define TRACE()             fprintf(stderr, "@ %s %d\n", __FUNCTION__, __LINE__);

#define CONTEXT_STARTED         lgw_context.is_started
#define CONTEXT_COM_TYPE        lgw_context.board_cfg.com_type
#define CONTEXT_COM_PATH        lgw_context.board_cfg.com_path
#define CONTEXT_LWAN_PUBLIC     lgw_context.board_cfg.lorawan_public
#define CONTEXT_BOARD           lgw_context.board_cfg
#define CONTEXT_RF_CHAIN        lgw_context.rf_chain_cfg
#define CONTEXT_IF_CHAIN        lgw_context.if_chain_cfg
#define CONTEXT_DEMOD           lgw_context.demod_cfg
#define CONTEXT_LORA_SERVICE    lgw_context.lora_service_cfg
#define CONTEXT_FSK             lgw_context.fsk_cfg
#define CONTEXT_TX_GAIN_LUT     lgw_context.tx_gain_lut
#define CONTEXT_FINE_TIMESTAMP  lgw_context.ftime_cfg
#define CONTEXT_SX1261          lgw_context.sx1261_cfg
#define CONTEXT_DEBUG           lgw_context.debug_cfg

/* -------------------------------------------------------------------------- */
/* --- PRIVATE CONSTANTS & TYPES -------------------------------------------- */

#define FW_VERSION_AGC_SX1250   10 /* Expected version of AGC firmware for sx1250 based gateway */
                                   /* v10 is same as v6 with improved channel check time for LBT */
#define FW_VERSION_AGC_SX125X   6  /* Expected version of AGC firmware for sx1255/sx1257 based gateway */
#define FW_VERSION_ARB          2  /* Expected version of arbiter firmware */

/* Useful bandwidth of SX125x radios to consider depending on channel bandwidth */
/* Note: the below values come from lab measurements. For any question, please contact Semtech support */
#define LGW_RF_RX_BANDWIDTH_125KHZ  1600000     /* for 125KHz channels */
#define LGW_RF_RX_BANDWIDTH_250KHZ  1600000     /* for 250KHz channels */
#define LGW_RF_RX_BANDWIDTH_500KHZ  1600000     /* for 500KHz channels */

#define LGW_RF_RX_FREQ_MIN          100E6
#define LGW_RF_RX_FREQ_MAX          1E9

/* Version string, used to identify the library version/options once compiled */
const char lgw_version_string[] = "Version: " LIBLORAGW_VERSION ";";

/* -------------------------------------------------------------------------- */
/* --- PRIVATE VARIABLES ---------------------------------------------------- */

#include "arb_fw.var"           /* text_arb_sx1302_13_Nov_3 */
#include "agc_fw_sx1250.var"    /* text_agc_sx1250_05_Juillet_2019_3 */
#include "agc_fw_sx1257.var"    /* text_agc_sx1257_19_Nov_1 */

/*
The following static variable holds the gateway configuration provided by the
user that need to be propagated in the drivers.

Parameters validity and coherency is verified by the _setconf functions and
the _start and _send functions assume they are valid.
*/
static lgw_context_t lgw_context = {
    .is_started = false,
    .board_cfg.com_type = LGW_COM_SPI,
    .board_cfg.com_path = "/dev/spidev0.0",
    .board_cfg.lorawan_public = true,
    .board_cfg.clksrc = 0,
    .board_cfg.full_duplex = false,
    .rf_chain_cfg = {{0}},
    .if_chain_cfg = {{0}},
    .demod_cfg = {
        .multisf_datarate = LGW_MULTI_SF_EN
    },
    .lora_service_cfg = {
        .enable = 0,    /* not used, handled by if_chain_cfg */
        .rf_chain = 0,  /* not used, handled by if_chain_cfg */
        .freq_hz = 0,   /* not used, handled by if_chain_cfg */
        .bandwidth = BW_250KHZ,
        .datarate = DR_LORA_SF7,
        .implicit_hdr = false,
        .implicit_payload_length = 0,
        .implicit_crc_en = 0,
        .implicit_coderate = 0
    },
    .fsk_cfg = {
        .enable = 0,    /* not used, handled by if_chain_cfg */
        .rf_chain = 0,  /* not used, handled by if_chain_cfg */
        .freq_hz = 0,   /* not used, handled by if_chain_cfg */
        .bandwidth = BW_125KHZ,
        .datarate = 50000,
        .sync_word_size = 3,
        .sync_word = 0xC194C1
    },
    .tx_gain_lut = {
        {
            .size = 1,
            .lut[0] = {
                .rf_power = 14,
                .dig_gain = 0,
                .pa_gain = 2,
                .dac_gain = 3,
                .mix_gain = 10,
                .offset_i = 0,
                .offset_q = 0,
                .pwr_idx = 0
            }
        },{
            .size = 1,
            .lut[0] = {
                .rf_power = 14,
                .dig_gain = 0,
                .pa_gain = 2,
                .dac_gain = 3,
                .mix_gain = 10,
                .offset_i = 0,
                .offset_q = 0,
                .pwr_idx = 0
            }
        }
    },
    .ftime_cfg = {
        .enable = false,
        .mode = LGW_FTIME_MODE_ALL_SF
    },
    .sx1261_cfg = {
        .enable = false,
        .spi_path = "/dev/spidev0.1",
        .rssi_offset = 0,
        .lbt_conf = {
            .rssi_target = 0,
            .nb_channel = 0,
            .channels = {{ 0 }}
        }
    },
    .debug_cfg = {
        .nb_ref_payload = 0,
    }
};

/* File handle to write debug logs */
FILE * log_file = NULL;

/* I2C temperature sensor handles */
static uint8_t ts_addr = 0xFF;

/* -------------------------------------------------------------------------- */
/* --- PRIVATE FUNCTIONS DECLARATION ---------------------------------------- */

int32_t lgw_sf_getval(int x);
int32_t lgw_bw_getval(int x);

static bool is_same_pkt(struct lgw_pkt_rx_s *p1, struct lgw_pkt_rx_s *p2);
static int remove_pkt(struct lgw_pkt_rx_s * p, uint8_t * nb_pkt, uint8_t pkt_index);
static int merge_packets(struct lgw_pkt_rx_s * p, uint8_t * nb_pkt);

/* -------------------------------------------------------------------------- */
/* --- PRIVATE FUNCTIONS DEFINITION ----------------------------------------- */

int32_t lgw_bw_getval(int x) {
    switch (x) {
        case BW_500KHZ: return 500000;
        case BW_250KHZ: return 250000;
        case BW_125KHZ: return 125000;
        default: return -1;
    }
}

/* ~~~~~~~~~~~~~~~~~~~~~~~~~~~~~~~~ */

int32_t lgw_sf_getval(int x) {
    switch (x) {
        case DR_LORA_SF5: return 5;
        case DR_LORA_SF6: return 6;
        case DR_LORA_SF7: return 7;
        case DR_LORA_SF8: return 8;
        case DR_LORA_SF9: return 9;
        case DR_LORA_SF10: return 10;
        case DR_LORA_SF11: return 11;
        case DR_LORA_SF12: return 12;
        default: return -1;
    }
}

/* ~~~~~~~~~~~~~~~~~~~~~~~~~~~~~~~~ */

static bool is_same_pkt(struct lgw_pkt_rx_s *p1, struct lgw_pkt_rx_s *p2) {
    if ((p1 != NULL) && (p2 != NULL)) {
        /* Criterias to determine if packets are identical:
            -- count_us should be equal or can have up to 24µs of difference (3 samples)
            -- channel should be same
            -- datarate should be same
            -- payload should be same
        */
        //if ((abs(p1->count_us - p2->count_us) <= 24) &&
        if (((p1->count_us >= p2->count_us && p1->count_us - p2->count_us <= 24) ||
             (p2->count_us >  p1->count_us && p2->count_us - p1->count_us <= 24)) &&
            (p1->if_chain == p2->if_chain) &&
            (p1->datarate == p2->datarate) &&
            (p1->size == p2->size) &&
            (memcmp(p1->payload, p2->payload, p1->size) == 0)) {

            return true;
        }
    }

    return false;
}

/* ~~~~~~~~~~~~~~~~~~~~~~~~~~~~~~~~ */

static int remove_pkt(struct lgw_pkt_rx_s * p, uint8_t * nb_pkt, uint8_t pkt_index) {
    /* Check input parameters */
    CHECK_NULL(p);
    CHECK_NULL(nb_pkt);
    if (pkt_index > ((*nb_pkt) - 1)) {
        printf("ERROR: failed to remove packet index %u\n", pkt_index);
        return -1;
    }

    /* Remove pkt from array, by replacing it with last packet of array */
    if (pkt_index == ((*nb_pkt) - 1)) {
        /* If we remove last element, just decrement nb packet counter */
        /* Do nothing */
    } else {
        /* Copy last packet onto the packet to be removed */
        memcpy(p + pkt_index, p + (*nb_pkt) - 1, sizeof(struct lgw_pkt_rx_s));
    }

    *nb_pkt -= 1;

    return 0;
}

/* ~~~~~~~~~~~~~~~~~~~~~~~~~~~~~~~~ */

int compare_pkt_tmst(const void *a, const void *b, void *arg)
{
    struct lgw_pkt_rx_s *p = (struct lgw_pkt_rx_s *)a;
    struct lgw_pkt_rx_s *q = (struct lgw_pkt_rx_s *)b;
    int *counter = (int *)arg;
    int p_count, q_count;

    p_count = p->count_us;
    q_count = q->count_us;

    if (p_count > q_count) {
        *counter = *counter + 1;
    }

    return (p_count - q_count);
}

/* ~~~~~~~~~~~~~~~~~~~~~~~~~~~~~~~~ */

static int merge_packets(struct lgw_pkt_rx_s * p, uint8_t * nb_pkt) {
    uint8_t cpt;
    int j, k, pkt_dup_idx, x;
#if DEBUG_HAL == 1
    int pkt_idx;
#endif
    bool dup_restart = false;
    int counter_qsort_swap = 0;

    /* Check input parameters */
    CHECK_NULL(p);
    CHECK_NULL(nb_pkt);

    /* Init number of packets in array before merge */
    cpt = *nb_pkt;

    /* --------------------------------------------- */
    /* ---------- For Debug only - START ----------- */
    if (cpt > 0) {
        DEBUG_MSG("<----- Searching for DUPLICATEs ------\n");
    }
    for (j = 0; j < cpt; j++) {
        DEBUG_PRINTF("  %d: tmst=%u SF=%u CRC_status=%d freq=%u chan=%u", j, p[j].count_us, p[j].datarate, p[j].status, p[j].freq_hz, p[j].if_chain);
        if (p[j].ftime_received == true) {
            DEBUG_PRINTF(" ftime=%u\n", p[j].ftime);
        } else {
            DEBUG_MSG   (" ftime=NONE\n");
        }
    }
    /* ---------- For Debug only - END ------------- */
    /* --------------------------------------------- */

    /* Remove duplicates */
    j = 0;
    while (j < cpt) {
        for (k = (j+1); k < cpt; k++) {
            /* Searching for duplicated packets:
                -- count_us should be equal or can have up to 24µs of difference (3 samples)
                -- channel should be same
                -- datarate should be same
                -- payload should be same
            */
            if (is_same_pkt( &p[j], &p[k])) {
                /* We keep the packet which has CRC checked */
                if ((p[j].status == STAT_CRC_OK) && (p[k].status == STAT_CRC_BAD)) {
                    pkt_dup_idx = k;
#if DEBUG_HAL == 1
                    pkt_idx = j;
#endif
                } else if ((p[j].status == STAT_CRC_BAD) && (p[k].status == STAT_CRC_OK)) {
                    pkt_dup_idx = j;
#if DEBUG_HAL == 1
                    pkt_idx = k;
#endif
                } else {
                    /* we keep the packet which has a fine timestamp */
                    if (p[j].ftime_received == true) {
                        pkt_dup_idx = k;
#if DEBUG_HAL == 1
                        pkt_idx = j;
#endif
                    } else {
                        pkt_dup_idx = j;
#if DEBUG_HAL == 1
                        pkt_idx = k;
#endif
                    }
                    /* sanity check */
                    if (((p[j].ftime_received == true) && (p[k].ftime_received == true)) ||
                        ((p[j].ftime_received == false) && (p[k].ftime_received == false))) {
                        DEBUG_MSG("WARNING: both duplicates have fine timestamps, or none has ? TBC\n");
                    }
                }
                /* pkt_dup_idx contains the index to be deleted */
                DEBUG_PRINTF("duplicate found %d:%d, deleting %d\n", pkt_idx, pkt_dup_idx, pkt_dup_idx);
                /* Remove duplicated packet from packet array */
                x = remove_pkt(p, &cpt, pkt_dup_idx);
                if (x != 0) {
                    printf("ERROR: failed to remove packet from array (%d)\n", x);
                }
                dup_restart = true;
                break;
            }
        }
        if (dup_restart == true) {
            /* Duplicate found, restart searching for duplicate from first element */
            j = 0;
            dup_restart = false;
#if 0
            printf( "restarting search for duplicate\n" ); /* Too verbose */
#endif
        } else {
            /* No duplicate found, continue... */
            j += 1;
#if 0
            printf( "no duplicate found\n" ); /* Too verbose */
#endif
        }
    }

    /* Sort the packet array by ascending counter_us value */
    qsort_r(p, cpt, sizeof(p[0]), compare_pkt_tmst, &counter_qsort_swap);
    DEBUG_PRINTF("%d elements swapped during sorting...\n", counter_qsort_swap);

    /* --------------------------------------------- */
    /* ---------- For Debug only - START ----------- */
    if (cpt > 0) {
        DEBUG_MSG("--\n");
    }
    for (j = 0; j < cpt; j++) {
        DEBUG_PRINTF("  %d: tmst=%u SF=%d CRC_status=%d freq=%u chan=%u", j, p[j].count_us, p[j].datarate, p[j].status, p[j].freq_hz, p[j].if_chain);
        if (p[j].ftime_received == true) {
            DEBUG_PRINTF(" ftime=%u\n", p[j].ftime);
        } else {
            DEBUG_MSG   (" ftime=NONE\n");
        }
    }
    if (cpt > 0) {
        DEBUG_MSG( " ------------------------------------>\n\n" );
    }
    /* ---------- For Debug only - END ------------- */
    /* --------------------------------------------- */

    /* Update number of packets contained in packet array */
    *nb_pkt = cpt;

    return 0;
}

/* -------------------------------------------------------------------------- */
/* --- PUBLIC FUNCTIONS DEFINITION ------------------------------------------ */

int lgw_board_setconf(struct lgw_conf_board_s * conf) {
    CHECK_NULL(conf);

    /* check if the concentrator is running */
    if (CONTEXT_STARTED == true) {
        DEBUG_MSG("ERROR: CONCENTRATOR IS RUNNING, STOP IT BEFORE TOUCHING CONFIGURATION\n");
        return LGW_HAL_ERROR;
    }

    /* Check input parameters */
    if ((conf->com_type != LGW_COM_SPI) && (conf->com_type != LGW_COM_USB)) {
        DEBUG_MSG("ERROR: WRONG COM TYPE\n");
        return LGW_HAL_ERROR;
    }

    /* set internal config according to parameters */
    CONTEXT_LWAN_PUBLIC = conf->lorawan_public;
    CONTEXT_BOARD.clksrc = conf->clksrc;
    CONTEXT_BOARD.full_duplex = conf->full_duplex;
    CONTEXT_COM_TYPE = conf->com_type;
    strncpy(CONTEXT_COM_PATH, conf->com_path, sizeof CONTEXT_COM_PATH);
    CONTEXT_COM_PATH[sizeof CONTEXT_COM_PATH - 1] = '\0'; /* ensure string termination */

    DEBUG_PRINTF("Note: board configuration: com_type: %s, com_path: %s, lorawan_public:%d, clksrc:%d, full_duplex:%d\n",   (CONTEXT_COM_TYPE == LGW_COM_SPI) ? "SPI" : "USB",
                                                                                                                            CONTEXT_COM_PATH,
                                                                                                                            CONTEXT_LWAN_PUBLIC,
                                                                                                                            CONTEXT_BOARD.clksrc,
                                                                                                                            CONTEXT_BOARD.full_duplex);

    return LGW_HAL_SUCCESS;
}

/* ~~~~~~~~~~~~~~~~~~~~~~~~~~~~~~~~ */

int lgw_rxrf_setconf(uint8_t rf_chain, struct lgw_conf_rxrf_s * conf) {
    CHECK_NULL(conf);

    /* check if the concentrator is running */
    if (CONTEXT_STARTED == true) {
        DEBUG_MSG("ERROR: CONCENTRATOR IS RUNNING, STOP IT BEFORE TOUCHING CONFIGURATION\n");
        return LGW_HAL_ERROR;
    }

    if (conf->enable == false) {
        /* nothing to do */
        DEBUG_PRINTF("Note: rf_chain %d disabled\n", rf_chain);
        return LGW_HAL_SUCCESS;
    }

    /* check input range (segfault prevention) */
    if (rf_chain >= LGW_RF_CHAIN_NB) {
        DEBUG_MSG("ERROR: NOT A VALID RF_CHAIN NUMBER\n");
        return LGW_HAL_ERROR;
    }

    /* check if radio type is supported */
    if ((conf->type != LGW_RADIO_TYPE_SX1255) && (conf->type != LGW_RADIO_TYPE_SX1257) && (conf->type != LGW_RADIO_TYPE_SX1250)) {
        DEBUG_PRINTF("ERROR: NOT A VALID RADIO TYPE (%d)\n", conf->type);
        return LGW_HAL_ERROR;
    }

    /* check if the radio central frequency is valid */
    if ((conf->freq_hz < LGW_RF_RX_FREQ_MIN) || (conf->freq_hz > LGW_RF_RX_FREQ_MAX)) {
        DEBUG_PRINTF("ERROR: NOT A VALID RADIO CENTER FREQUENCY, PLEASE CHECK IF IT HAS BEEN GIVEN IN HZ (%u)\n", conf->freq_hz);
        return LGW_HAL_ERROR;
    }

    /* set internal config according to parameters */
    CONTEXT_RF_CHAIN[rf_chain].enable = conf->enable;
    CONTEXT_RF_CHAIN[rf_chain].freq_hz = conf->freq_hz;
    CONTEXT_RF_CHAIN[rf_chain].rssi_offset = conf->rssi_offset;
    CONTEXT_RF_CHAIN[rf_chain].rssi_tcomp.coeff_a = conf->rssi_tcomp.coeff_a;
    CONTEXT_RF_CHAIN[rf_chain].rssi_tcomp.coeff_b = conf->rssi_tcomp.coeff_b;
    CONTEXT_RF_CHAIN[rf_chain].rssi_tcomp.coeff_c = conf->rssi_tcomp.coeff_c;
    CONTEXT_RF_CHAIN[rf_chain].rssi_tcomp.coeff_d = conf->rssi_tcomp.coeff_d;
    CONTEXT_RF_CHAIN[rf_chain].rssi_tcomp.coeff_e = conf->rssi_tcomp.coeff_e;
    CONTEXT_RF_CHAIN[rf_chain].type = conf->type;
    CONTEXT_RF_CHAIN[rf_chain].tx_enable = conf->tx_enable;
    CONTEXT_RF_CHAIN[rf_chain].single_input_mode = conf->single_input_mode;

    DEBUG_PRINTF("Note: rf_chain %d configuration; en:%d freq:%d rssi_offset:%f radio_type:%d tx_enable:%d single_input_mode:%d\n",  rf_chain,
                                                                                                                CONTEXT_RF_CHAIN[rf_chain].enable,
                                                                                                                CONTEXT_RF_CHAIN[rf_chain].freq_hz,
                                                                                                                CONTEXT_RF_CHAIN[rf_chain].rssi_offset,
                                                                                                                CONTEXT_RF_CHAIN[rf_chain].type,
                                                                                                                CONTEXT_RF_CHAIN[rf_chain].tx_enable,
                                                                                                                CONTEXT_RF_CHAIN[rf_chain].single_input_mode);

    return LGW_HAL_SUCCESS;
}

/* ~~~~~~~~~~~~~~~~~~~~~~~~~~~~~~~~ */
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
